simonyiszk/open-hf-sdr/DOC/if3_filter.asc

C1: cap; 166p
C2: cap; 940p
C3: cap; 18p
C4: cap; 213p
L1: ind; 2.2µ
L2: ind; 10µ
L3: ind; 1.1µ
L5: ind; 220n
RL: res; 50
V1: voltage; ""; AC 1 0; Rser=1500
Named nets: 0
.ac lin 1001 5Meg 15Meg
.net I(RL) V1
4th Order Inverse Chebyshev Bandpass
Conventional, Series First
Lower Cutoff Freq. = 35.25 MHz; Upper Cutoff Freq. = 38.75 MHz
Stopband Attenuation = 50.00 dB

rf-tools.com | Dec 27 2020 18:43
.step param C 2.2u 2.4u 200n
