simonyiszk/open-hf-sdr/DOC/cb_diff_amp.asc

C1: cap; 56p
C2: cap; 22p
C3: cap; 270p
C4: cap; 33p
C5: cap; 33p
C6: cap; 330p
C7: cap; 330p
C8: cap; 10µ
C9: cap; 7.96p
L1: ind; 3.3µ
L2: ind; 3.3µ
L3: ind; 10µ
L4: ind; 10µ
L5: ind; 1.5µ
L6: ind; 150n
L7: ind; 150n
L8: ind; 19.65µ
L9: ind; 19.65µ
Q1: npn
Q2: npn
R1: res; 2k
R2: res; 1500
R3: res; 1500
R4: res; 10k
R5: res; 10k
V1: voltage; ""; AC 1
V2: voltage; ""; AC 1
V3: voltage; 2.8
V4: voltage; 5
Named nets: In+, In-, 0, Out+, Out-
.ac lin 100meg 5meg 15meg
;op lin 1meg 5meg 15meg
