simonyiszk/open-hf-sdr/vivado/ha5kfu_ws2/ha5kfu_ws2.srcs/sources_1/bd/top/ip/top_dds_compiler_0_0/synth/top_dds_compiler_0_0.vhd

-- (c) Copyright 1995-2021 Xilinx, Inc. All rights reserved.
-- 
-- This file contains confidential and proprietary information
-- of Xilinx, Inc. and is protected under U.S. and
-- international copyright and other intellectual property
-- laws.
-- 
-- DISCLAIMER
-- This disclaimer is not a license and does not grant any
-- rights to the materials distributed herewith. Except as
-- otherwise provided in a valid license issued to you by
-- Xilinx, and to the maximum extent permitted by applicable
-- law: (1) THESE MATERIALS ARE MADE AVAILABLE "AS IS" AND
-- WITH ALL FAULTS, AND XILINX HEREBY DISCLAIMS ALL WARRANTIES
-- AND CONDITIONS, EXPRESS, IMPLIED, OR STATUTORY, INCLUDING
-- BUT NOT LIMITED TO WARRANTIES OF MERCHANTABILITY, NON-
-- INFRINGEMENT, OR FITNESS FOR ANY PARTICULAR PURPOSE; and
-- (2) Xilinx shall not be liable (whether in contract or tort,
-- including negligence, or under any other theory of
-- liability) for any loss or damage of any kind or nature
-- related to, arising under or in connection with these
-- materials, including for any direct, or any indirect,
-- special, incidental, or consequential loss or damage
-- (including loss of data, profits, goodwill, or any type of
-- loss or damage suffered as a result of any action brought
-- by a third party) even if such damage or loss was
-- reasonably foreseeable or Xilinx had been advised of the
-- possibility of the same.
-- 
-- CRITICAL APPLICATIONS
-- Xilinx products are not designed or intended to be fail-
-- safe, or for use in any application requiring fail-safe
-- performance, such as life-support or safety devices or
-- systems, Class III medical devices, nuclear facilities,
-- applications related to the deployment of airbags, or any
-- other applications that could lead to death, personal
-- injury, or severe property or environmental damage
-- (individually and collectively, "Critical
-- Applications"). Customer assumes the sole risk and
-- liability of any use of Xilinx products in Critical
-- Applications, subject only to applicable laws and
-- regulations governing limitations on product liability.
-- 
-- THIS COPYRIGHT NOTICE AND DISCLAIMER MUST BE RETAINED AS
-- PART OF THIS FILE AT ALL TIMES.
-- 
-- DO NOT MODIFY THIS FILE.

-- IP VLNV: xilinx.com:ip:dds_compiler:6.0
-- IP Revision: 20

LIBRARY ieee;
USE ieee.std_logic_1164.ALL;
USE ieee.numeric_std.ALL;

LIBRARY dds_compiler_v6_0_20;
USE dds_compiler_v6_0_20.dds_compiler_v6_0_20;

ENTITY top_dds_compiler_0_0 IS
  PORT (
    aclk : IN STD_LOGIC;
    s_axis_config_tvalid : IN STD_LOGIC;
    s_axis_config_tdata : IN STD_LOGIC_VECTOR(63 DOWNTO 0);
    m_axis_data_tvalid : OUT STD_LOGIC;
    m_axis_data_tdata : OUT STD_LOGIC_VECTOR(15 DOWNTO 0);
    m_axis_phase_tvalid : OUT STD_LOGIC;
    m_axis_phase_tdata : OUT STD_LOGIC_VECTOR(31 DOWNTO 0)
  );
END top_dds_compiler_0_0;

ARCHITECTURE top_dds_compiler_0_0_arch OF top_dds_compiler_0_0 IS
  ATTRIBUTE DowngradeIPIdentifiedWarnings : STRING;
  ATTRIBUTE DowngradeIPIdentifiedWarnings OF top_dds_compiler_0_0_arch: ARCHITECTURE IS "yes";
  COMPONENT dds_compiler_v6_0_20 IS
    GENERIC (
      C_XDEVICEFAMILY : STRING;
      C_MODE_OF_OPERATION : INTEGER;
      C_MODULUS : INTEGER;
      C_ACCUMULATOR_WIDTH : INTEGER;
      C_CHANNELS : INTEGER;
      C_HAS_PHASE_OUT : INTEGER;
      C_HAS_PHASEGEN : INTEGER;
      C_HAS_SINCOS : INTEGER;
      C_LATENCY : INTEGER;
      C_MEM_TYPE : INTEGER;
      C_NEGATIVE_COSINE : INTEGER;
      C_NEGATIVE_SINE : INTEGER;
      C_NOISE_SHAPING : INTEGER;
      C_OUTPUTS_REQUIRED : INTEGER;
      C_OUTPUT_FORM : INTEGER;
      C_OUTPUT_WIDTH : INTEGER;
      C_PHASE_ANGLE_WIDTH : INTEGER;
      C_PHASE_INCREMENT : INTEGER;
      C_PHASE_INCREMENT_VALUE : STRING;
      C_RESYNC : INTEGER;
      C_PHASE_OFFSET : INTEGER;
      C_PHASE_OFFSET_VALUE : STRING;
      C_OPTIMISE_GOAL : INTEGER;
      C_USE_DSP48 : INTEGER;
      C_POR_MODE : INTEGER;
      C_AMPLITUDE : INTEGER;
      C_HAS_ACLKEN : INTEGER;
      C_HAS_ARESETN : INTEGER;
      C_HAS_TLAST : INTEGER;
      C_HAS_TREADY : INTEGER;
      C_HAS_S_PHASE : INTEGER;
      C_S_PHASE_TDATA_WIDTH : INTEGER;
      C_S_PHASE_HAS_TUSER : INTEGER;
      C_S_PHASE_TUSER_WIDTH : INTEGER;
      C_HAS_S_CONFIG : INTEGER;
      C_S_CONFIG_SYNC_MODE : INTEGER;
      C_S_CONFIG_TDATA_WIDTH : INTEGER;
      C_HAS_M_DATA : INTEGER;
      C_M_DATA_TDATA_WIDTH : INTEGER;
      C_M_DATA_HAS_TUSER : INTEGER;
      C_M_DATA_TUSER_WIDTH : INTEGER;
      C_HAS_M_PHASE : INTEGER;
      C_M_PHASE_TDATA_WIDTH : INTEGER;
      C_M_PHASE_HAS_TUSER : INTEGER;
      C_M_PHASE_TUSER_WIDTH : INTEGER;
      C_DEBUG_INTERFACE : INTEGER;
      C_CHAN_WIDTH : INTEGER
    );
    PORT (
      aclk : IN STD_LOGIC;
      aclken : IN STD_LOGIC;
      aresetn : IN STD_LOGIC;
      s_axis_phase_tvalid : IN STD_LOGIC;
      s_axis_phase_tready : OUT STD_LOGIC;
      s_axis_phase_tdata : IN STD_LOGIC_VECTOR(0 DOWNTO 0);
      s_axis_phase_tlast : IN STD_LOGIC;
      s_axis_phase_tuser : IN STD_LOGIC_VECTOR(0 DOWNTO 0);
      s_axis_config_tvalid : IN STD_LOGIC;
      s_axis_config_tready : OUT STD_LOGIC;
      s_axis_config_tdata : IN STD_LOGIC_VECTOR(63 DOWNTO 0);
      s_axis_config_tlast : IN STD_LOGIC;
      m_axis_data_tvalid : OUT STD_LOGIC;
      m_axis_data_tready : IN STD_LOGIC;
      m_axis_data_tdata : OUT STD_LOGIC_VECTOR(15 DOWNTO 0);
      m_axis_data_tlast : OUT STD_LOGIC;
      m_axis_data_tuser : OUT STD_LOGIC_VECTOR(0 DOWNTO 0);
      m_axis_phase_tvalid : OUT STD_LOGIC;
      m_axis_phase_tready : IN STD_LOGIC;
      m_axis_phase_tdata : OUT STD_LOGIC_VECTOR(31 DOWNTO 0);
      m_axis_phase_tlast : OUT STD_LOGIC;
      m_axis_phase_tuser : OUT STD_LOGIC_VECTOR(0 DOWNTO 0);
      event_pinc_invalid : OUT STD_LOGIC;
      event_poff_invalid : OUT STD_LOGIC;
      event_phase_in_invalid : OUT STD_LOGIC;
      event_s_phase_tlast_missing : OUT STD_LOGIC;
      event_s_phase_tlast_unexpected : OUT STD_LOGIC;
      event_s_phase_chanid_incorrect : OUT STD_LOGIC;
      event_s_config_tlast_missing : OUT STD_LOGIC;
      event_s_config_tlast_unexpected : OUT STD_LOGIC
    );
  END COMPONENT dds_compiler_v6_0_20;
  ATTRIBUTE X_CORE_INFO : STRING;
  ATTRIBUTE X_CORE_INFO OF top_dds_compiler_0_0_arch: ARCHITECTURE IS "dds_compiler_v6_0_20,Vivado 2020.2";
  ATTRIBUTE CHECK_LICENSE_TYPE : STRING;
  ATTRIBUTE CHECK_LICENSE_TYPE OF top_dds_compiler_0_0_arch : ARCHITECTURE IS "top_dds_compiler_0_0,dds_compiler_v6_0_20,{}";
  ATTRIBUTE CORE_GENERATION_INFO : STRING;
  ATTRIBUTE CORE_GENERATION_INFO OF top_dds_compiler_0_0_arch: ARCHITECTURE IS "top_dds_compiler_0_0,dds_compiler_v6_0_20,{x_ipProduct=Vivado 2020.2,x_ipVendor=xilinx.com,x_ipLibrary=ip,x_ipName=dds_compiler,x_ipVersion=6.0,x_ipCoreRevision=20,x_ipLanguage=VERILOG,x_ipSimLanguage=MIXED,C_XDEVICEFAMILY=spartan7,C_MODE_OF_OPERATION=0,C_MODULUS=9,C_ACCUMULATOR_WIDTH=27,C_CHANNELS=1,C_HAS_PHASE_OUT=1,C_HAS_PHASEGEN=1,C_HAS_SINCOS=1,C_LATENCY=4,C_MEM_TYPE=1,C_NEGATIVE_COSINE=0,C_NEGATIVE_SINE=0,C_NOISE_SHAPING=0,C_OUTPUTS_REQUIRED=2,C_OUTPUT_FORM=0,C_OUTPUT_WIDTH=8,C_PHASE_ANGLE" & 
"_WIDTH=8,C_PHASE_INCREMENT=1,C_PHASE_INCREMENT_VALUE=0_0_0_0_0_0_0_0_0_0_0_0_0_0_0_0,C_RESYNC=0,C_PHASE_OFFSET=1,C_PHASE_OFFSET_VALUE=0_0_0_0_0_0_0_0_0_0_0_0_0_0_0_0,C_OPTIMISE_GOAL=0,C_USE_DSP48=0,C_POR_MODE=0,C_AMPLITUDE=0,C_HAS_ACLKEN=0,C_HAS_ARESETN=0,C_HAS_TLAST=0,C_HAS_TREADY=0,C_HAS_S_PHASE=0,C_S_PHASE_TDATA_WIDTH=1,C_S_PHASE_HAS_TUSER=0,C_S_PHASE_TUSER_WIDTH=1,C_HAS_S_CONFIG=1,C_S_CONFIG_SYNC_MODE=0,C_S_CONFIG_TDATA_WIDTH=64,C_HAS_M_DATA=1,C_M_DATA_TDATA_WIDTH=16,C_M_DATA_HAS_TUSER=0,C_M" & 
"_DATA_TUSER_WIDTH=1,C_HAS_M_PHASE=1,C_M_PHASE_TDATA_WIDTH=32,C_M_PHASE_HAS_TUSER=0,C_M_PHASE_TUSER_WIDTH=1,C_DEBUG_INTERFACE=0,C_CHAN_WIDTH=1}";
  ATTRIBUTE X_INTERFACE_INFO : STRING;
  ATTRIBUTE X_INTERFACE_PARAMETER : STRING;
  ATTRIBUTE X_INTERFACE_INFO OF m_axis_phase_tdata: SIGNAL IS "xilinx.com:interface:axis:1.0 M_AXIS_PHASE TDATA";
  ATTRIBUTE X_INTERFACE_PARAMETER OF m_axis_phase_tvalid: SIGNAL IS "XIL_INTERFACENAME M_AXIS_PHASE, TDATA_NUM_BYTES 4, TDEST_WIDTH 0, TID_WIDTH 0, TUSER_WIDTH 0, HAS_TREADY 0, HAS_TSTRB 0, HAS_TKEEP 0, HAS_TLAST 0, FREQ_HZ 125000000, PHASE 0.000, CLK_DOMAIN top_clk, LAYERED_METADATA xilinx.com:interface:datatypes:1.0 {TDATA {datatype {name {attribs {resolve_type immediate dependency {} format string minimum {} maximum {}} value {}} bitwidth {attribs {resolve_type automatic dependency {} format long minimum {} maximum {}} value 27} bitoffset {attribs {resolve_typ" & 
"e immediate dependency {} format long minimum {} maximum {}} value 0} array_type {name {attribs {resolve_type immediate dependency {} format string minimum {} maximum {}} value chan} size {attribs {resolve_type generated dependency chan_size format long minimum {} maximum {}} value 1} stride {attribs {resolve_type generated dependency chan_stride format long minimum {} maximum {}} value 32} datatype {name {attribs {resolve_type immediate dependency {} format string minimum {} maximum {}} value {" & 
"}} bitwidth {attribs {resolve_type automatic dependency {} format long minimum {} maximum {}} value 27} bitoffset {attribs {resolve_type immediate dependency {} format long minimum {} maximum {}} value 0} struct {field_phase_out {name {attribs {resolve_type immediate dependency {} format string minimum {} maximum {}} value phase_out} enabled {attribs {resolve_type immediate dependency {} format bool minimum {} maximum {}} value true} datatype {name {attribs {resolve_type immediate dependency {} " & 
"format string minimum {} maximum {}} value {}} bitwidth {attribs {resolve_type generated dependency phase_width format long minimum {} maximum {}} value 27} bitoffset {attribs {resolve_type immediate dependency {} format long minimum {} maximum {}} value 0} real {fixed {fractwidth {attribs {resolve_type generated dependency phase_fractwidth format long minimum {} maximum {}} value 27} signed {attribs {resolve_type immediate dependency {} format bool minimum {} maximum {}} value false}}}}}}}}}} T" & 
"DATA_WIDTH 32 TUSER {datatype {name {attribs {resolve_type immediate dependency {} format string minimum {} maximum {}} value {}} bitwidth {attribs {resolve_type automatic dependency {} format long minimum {} maximum {}} value 0} bitoffset {attribs {resolve_type immediate dependency {} format long minimum {} maximum {}} value 0} struct {field_chanid {name {attribs {resolve_type immediate dependency {} format string minimum {} maximum {}} value chanid} enabled {attribs {resolve_type generated dep" & 
"endency chanid_enabled format bool minimum {} maximum {}} value false} datatype {name {attribs {resolve_type immediate dependency {} format string minimum {} maximum {}} value {}} bitwidth {attribs {resolve_type generated dependency chanid_width format long minimum {} maximum {}} value 0} bitoffset {attribs {resolve_type immediate dependency {} format long minimum {} maximum {}} value 0} integer {signed {attribs {resolve_type immediate dependency {} format bool minimum {} maximum {}} value false" & 
"}}}} field_user {name {attribs {resolve_type immediate dependency {} format string minimum {} maximum {}} value user} enabled {attribs {resolve_type generated dependency user_enabled format bool minimum {} maximum {}} value false} datatype {name {attribs {resolve_type immediate dependency {} format string minimum {} maximum {}} value {}} bitwidth {attribs {resolve_type generated dependency user_width format long minimum {} maximum {}} value 0} bitoffset {attribs {resolve_type generated dependenc" & 
"y user_offset format long minimum {} maximum {}} value 0}}}}}} TUSER_WIDTH 0}, INSERT_VIP 0";
  ATTRIBUTE X_INTERFACE_INFO OF m_axis_phase_tvalid: SIGNAL IS "xilinx.com:interface:axis:1.0 M_AXIS_PHASE TVALID";
  ATTRIBUTE X_INTERFACE_INFO OF m_axis_data_tdata: SIGNAL IS "xilinx.com:interface:axis:1.0 M_AXIS_DATA TDATA";
  ATTRIBUTE X_INTERFACE_PARAMETER OF m_axis_data_tvalid: SIGNAL IS "XIL_INTERFACENAME M_AXIS_DATA, TDATA_NUM_BYTES 2, TDEST_WIDTH 0, TID_WIDTH 0, TUSER_WIDTH 0, HAS_TREADY 0, HAS_TSTRB 0, HAS_TKEEP 0, HAS_TLAST 0, FREQ_HZ 125000000, PHASE 0.000, CLK_DOMAIN top_clk, LAYERED_METADATA xilinx.com:interface:datatypes:1.0 {TDATA {datatype {name {attribs {resolve_type immediate dependency {} format string minimum {} maximum {}} value {}} bitwidth {attribs {resolve_type automatic dependency {} format long minimum {} maximum {}} value 16} bitoffset {attribs {resolve_type" & 
" immediate dependency {} format long minimum {} maximum {}} value 0} array_type {name {attribs {resolve_type immediate dependency {} format string minimum {} maximum {}} value chan} size {attribs {resolve_type generated dependency chan_size format long minimum {} maximum {}} value 1} stride {attribs {resolve_type generated dependency chan_stride format long minimum {} maximum {}} value 16} datatype {name {attribs {resolve_type immediate dependency {} format string minimum {} maximum {}} value {}" & 
"} bitwidth {attribs {resolve_type automatic dependency {} format long minimum {} maximum {}} value 16} bitoffset {attribs {resolve_type immediate dependency {} format long minimum {} maximum {}} value 0} struct {field_cosine {name {attribs {resolve_type immediate dependency {} format string minimum {} maximum {}} value cosine} enabled {attribs {resolve_type generated dependency cosine_enabled format bool minimum {} maximum {}} value true} datatype {name {attribs {resolve_type immediate dependenc" & 
"y {} format string minimum {} maximum {}} value {}} bitwidth {attribs {resolve_type generated dependency cosine_width format long minimum {} maximum {}} value 8} bitoffset {attribs {resolve_type immediate dependency {} format long minimum {} maximum {}} value 0} real {fixed {fractwidth {attribs {resolve_type generated dependency cosine_fractwidth format long minimum {} maximum {}} value 7} signed {attribs {resolve_type immediate dependency {} format bool minimum {} maximum {}} value true}}}}} fi" & 
"eld_sine {name {attribs {resolve_type immediate dependency {} format string minimum {} maximum {}} value sine} enabled {attribs {resolve_type generated dependency sine_enabled format bool minimum {} maximum {}} value true} datatype {name {attribs {resolve_type immediate dependency {} format string minimum {} maximum {}} value {}} bitwidth {attribs {resolve_type generated dependency sine_width format long minimum {} maximum {}} value 8} bitoffset {attribs {resolve_type generated dependency sine_o" & 
"ffset format long minimum {} maximum {}} value 8} real {fixed {fractwidth {attribs {resolve_type generated dependency sine_fractwidth format long minimum {} maximum {}} value 7} signed {attribs {resolve_type immediate dependency {} format bool minimum {} maximum {}} value true}}}}}}}}}} TDATA_WIDTH 16 TUSER {datatype {name {attribs {resolve_type immediate dependency {} format string minimum {} maximum {}} value {}} bitwidth {attribs {resolve_type automatic dependency {} format long minimum {} ma" & 
"ximum {}} value 0} bitoffset {attribs {resolve_type immediate dependency {} format long minimum {} maximum {}} value 0} struct {field_chanid {name {attribs {resolve_type immediate dependency {} format string minimum {} maximum {}} value chanid} enabled {attribs {resolve_type generated dependency chanid_enabled format bool minimum {} maximum {}} value false} datatype {name {attribs {resolve_type immediate dependency {} format string minimum {} maximum {}} value {}} bitwidth {attribs {resolve_type" & 
" generated dependency chanid_width format long minimum {} maximum {}} value 0} bitoffset {attribs {resolve_type immediate dependency {} format long minimum {} maximum {}} value 0} integer {signed {attribs {resolve_type immediate dependency {} format bool minimum {} maximum {}} value false}}}} field_user {name {attribs {resolve_type immediate dependency {} format string minimum {} maximum {}} value user} enabled {attribs {resolve_type generated dependency user_enabled format bool minimum {} maxim" & 
"um {}} value false} datatype {name {attribs {resolve_type immediate dependency {} format string minimum {} maximum {}} value {}} bitwidth {attribs {resolve_type generated dependency user_width format long minimum {} maximum {}} value 0} bitoffset {attribs {resolve_type generated dependency user_offset format long minimum {} maximum {}} value 0}}}}}} TUSER_WIDTH 0}, INSERT_VIP 0";
  ATTRIBUTE X_INTERFACE_INFO OF m_axis_data_tvalid: SIGNAL IS "xilinx.com:interface:axis:1.0 M_AXIS_DATA TVALID";
  ATTRIBUTE X_INTERFACE_INFO OF s_axis_config_tdata: SIGNAL IS "xilinx.com:interface:axis:1.0 S_AXIS_CONFIG TDATA";
  ATTRIBUTE X_INTERFACE_PARAMETER OF s_axis_config_tvalid: SIGNAL IS "XIL_INTERFACENAME S_AXIS_CONFIG, TDATA_NUM_BYTES 8, TDEST_WIDTH 0, TID_WIDTH 0, TUSER_WIDTH 0, HAS_TREADY 0, HAS_TSTRB 0, HAS_TKEEP 0, HAS_TLAST 0, FREQ_HZ 125000000, PHASE 0.000, CLK_DOMAIN top_clk, LAYERED_METADATA undef, INSERT_VIP 0";
  ATTRIBUTE X_INTERFACE_INFO OF s_axis_config_tvalid: SIGNAL IS "xilinx.com:interface:axis:1.0 S_AXIS_CONFIG TVALID";
  ATTRIBUTE X_INTERFACE_PARAMETER OF aclk: SIGNAL IS "XIL_INTERFACENAME aclk_intf, ASSOCIATED_BUSIF M_AXIS_PHASE:S_AXIS_CONFIG:M_AXIS_DATA:S_AXIS_PHASE, ASSOCIATED_RESET aresetn, ASSOCIATED_CLKEN aclken, FREQ_HZ 125000000, FREQ_TOLERANCE_HZ 0, PHASE 0.000, CLK_DOMAIN top_clk, INSERT_VIP 0";
  ATTRIBUTE X_INTERFACE_INFO OF aclk: SIGNAL IS "xilinx.com:signal:clock:1.0 aclk_intf CLK";
BEGIN
  U0 : dds_compiler_v6_0_20
    GENERIC MAP (
      C_XDEVICEFAMILY => "spartan7",
      C_MODE_OF_OPERATION => 0,
      C_MODULUS => 9,
      C_ACCUMULATOR_WIDTH => 27,
      C_CHANNELS => 1,
      C_HAS_PHASE_OUT => 1,
      C_HAS_PHASEGEN => 1,
      C_HAS_SINCOS => 1,
      C_LATENCY => 4,
      C_MEM_TYPE => 1,
      C_NEGATIVE_COSINE => 0,
      C_NEGATIVE_SINE => 0,
      C_NOISE_SHAPING => 0,
      C_OUTPUTS_REQUIRED => 2,
      C_OUTPUT_FORM => 0,
      C_OUTPUT_WIDTH => 8,
      C_PHASE_ANGLE_WIDTH => 8,
      C_PHASE_INCREMENT => 1,
      C_PHASE_INCREMENT_VALUE => "0,0,0,0,0,0,0,0,0,0,0,0,0,0,0,0",
      C_RESYNC => 0,
      C_PHASE_OFFSET => 1,
      C_PHASE_OFFSET_VALUE => "0,0,0,0,0,0,0,0,0,0,0,0,0,0,0,0",
      C_OPTIMISE_GOAL => 0,
      C_USE_DSP48 => 0,
      C_POR_MODE => 0,
      C_AMPLITUDE => 0,
      C_HAS_ACLKEN => 0,
      C_HAS_ARESETN => 0,
      C_HAS_TLAST => 0,
      C_HAS_TREADY => 0,
      C_HAS_S_PHASE => 0,
      C_S_PHASE_TDATA_WIDTH => 1,
      C_S_PHASE_HAS_TUSER => 0,
      C_S_PHASE_TUSER_WIDTH => 1,
      C_HAS_S_CONFIG => 1,
      C_S_CONFIG_SYNC_MODE => 0,
      C_S_CONFIG_TDATA_WIDTH => 64,
      C_HAS_M_DATA => 1,
      C_M_DATA_TDATA_WIDTH => 16,
      C_M_DATA_HAS_TUSER => 0,
      C_M_DATA_TUSER_WIDTH => 1,
      C_HAS_M_PHASE => 1,
      C_M_PHASE_TDATA_WIDTH => 32,
      C_M_PHASE_HAS_TUSER => 0,
      C_M_PHASE_TUSER_WIDTH => 1,
      C_DEBUG_INTERFACE => 0,
      C_CHAN_WIDTH => 1
    )
    PORT MAP (
      aclk => aclk,
      aclken => '1',
      aresetn => '1',
      s_axis_phase_tvalid => '0',
      s_axis_phase_tdata => STD_LOGIC_VECTOR(TO_UNSIGNED(0, 1)),
      s_axis_phase_tlast => '0',
      s_axis_phase_tuser => STD_LOGIC_VECTOR(TO_UNSIGNED(0, 1)),
      s_axis_config_tvalid => s_axis_config_tvalid,
      s_axis_config_tdata => s_axis_config_tdata,
      s_axis_config_tlast => '0',
      m_axis_data_tvalid => m_axis_data_tvalid,
      m_axis_data_tready => '0',
      m_axis_data_tdata => m_axis_data_tdata,
      m_axis_phase_tvalid => m_axis_phase_tvalid,
      m_axis_phase_tready => '0',
      m_axis_phase_tdata => m_axis_phase_tdata
    );
END top_dds_compiler_0_0_arch;
