simonyiszk/open-hf-sdr/vivado/ha5kfu_ws2/ha5kfu_ws2.srcs/sources_1/bd/top/ip/top_c_addsub_0_0/top_c_addsub_0_0_stub.vhdl

-- Copyright 1986-2020 Xilinx, Inc. All Rights Reserved.
-- --------------------------------------------------------------------------------
-- Tool Version: Vivado v.2020.2 (win64) Build 3064766 Wed Nov 18 09:12:45 MST 2020
-- Date        : Fri Feb 12 23:06:54 2021
-- Host        : RemoteApp running 64-bit major release  (build 9200)
-- Command     : write_vhdl -force -mode synth_stub -rename_top top_c_addsub_0_0 -prefix
--               top_c_addsub_0_0_ top_c_addsub_0_0_stub.vhdl
-- Design      : top_c_addsub_0_0
-- Purpose     : Stub declaration of top-level module interface
-- Device      : xc7s6ftgb196-1
-- --------------------------------------------------------------------------------
library IEEE;
use IEEE.STD_LOGIC_1164.ALL;

entity top_c_addsub_0_0 is
  Port ( 
    A : in STD_LOGIC_VECTOR ( 12 downto 0 );
    B : in STD_LOGIC_VECTOR ( 12 downto 0 );
    CLK : in STD_LOGIC;
    S : out STD_LOGIC_VECTOR ( 13 downto 0 )
  );

end top_c_addsub_0_0;

architecture stub of top_c_addsub_0_0 is
attribute syn_black_box : boolean;
attribute black_box_pad_pin : string;
attribute syn_black_box of stub : architecture is true;
attribute black_box_pad_pin of stub : architecture is "A[12:0],B[12:0],CLK,S[13:0]";
attribute x_core_info : string;
attribute x_core_info of stub : architecture is "c_addsub_v12_0_14,Vivado 2020.2";
begin
end;
