simonyiszk/open-hf-sdr/vivado/ha5kfu_ws2/ha5kfu_ws2.srcs/sources_1/bd/top_design/ip/top_design_mult_gen_0_3/top_design_mult_gen_0_3_stub.vhdl

-- Copyright 1986-2020 Xilinx, Inc. All Rights Reserved.
-- --------------------------------------------------------------------------------
-- Tool Version: Vivado v.2020.2 (win64) Build 3064766 Wed Nov 18 09:12:45 MST 2020
-- Date        : Fri Feb 12 22:11:44 2021
-- Host        : RemoteApp running 64-bit major release  (build 9200)
-- Command     : write_vhdl -force -mode synth_stub -rename_top top_design_mult_gen_0_3 -prefix
--               top_design_mult_gen_0_3_ top_design_mult_gen_0_1_stub.vhdl
-- Design      : top_design_mult_gen_0_1
-- Purpose     : Stub declaration of top-level module interface
-- Device      : xc7z010clg400-1
-- --------------------------------------------------------------------------------
library IEEE;
use IEEE.STD_LOGIC_1164.ALL;

entity top_design_mult_gen_0_3 is
  Port ( 
    CLK : in STD_LOGIC;
    A : in STD_LOGIC_VECTOR ( 13 downto 0 );
    B : in STD_LOGIC_VECTOR ( 7 downto 0 );
    P : out STD_LOGIC_VECTOR ( 12 downto 0 )
  );

end top_design_mult_gen_0_3;

architecture stub of top_design_mult_gen_0_3 is
attribute syn_black_box : boolean;
attribute black_box_pad_pin : string;
attribute syn_black_box of stub : architecture is true;
attribute black_box_pad_pin of stub : architecture is "CLK,A[13:0],B[7:0],P[12:0]";
attribute x_core_info : string;
attribute x_core_info of stub : architecture is "mult_gen_v12_0_16,Vivado 2020.2";
begin
end;
