simonyiszk/open-hf-sdr/vivado/ha5kfu_ws2/ha5kfu_ws2.srcs/sources_1/bd/top/ip/top_c_addsub_0_0/top_c_addsub_0_0_sim_netlist.v

// Copyright 1986-2020 Xilinx, Inc. All Rights Reserved.
// --------------------------------------------------------------------------------
// Tool Version: Vivado v.2020.2 (win64) Build 3064766 Wed Nov 18 09:12:45 MST 2020
// Date        : Fri Feb 12 23:06:54 2021
// Host        : RemoteApp running 64-bit major release  (build 9200)
// Command     : write_verilog -force -mode funcsim -rename_top top_c_addsub_0_0 -prefix
//               top_c_addsub_0_0_ top_c_addsub_0_0_sim_netlist.v
// Design      : top_c_addsub_0_0
// Purpose     : This verilog netlist is a functional simulation representation of the design and should not be modified
//               or synthesized. This netlist cannot be used for SDF annotated simulation.
// Device      : xc7s6ftgb196-1
// --------------------------------------------------------------------------------
`timescale 1 ps / 1 ps

(* CHECK_LICENSE_TYPE = "top_c_addsub_0_0,c_addsub_v12_0_14,{}" *) (* downgradeipidentifiedwarnings = "yes" *) (* x_core_info = "c_addsub_v12_0_14,Vivado 2020.2" *) 
(* NotValidForBitStream *)
module top_c_addsub_0_0
   (A,
    B,
    CLK,
    S);
  (* x_interface_info = "xilinx.com:signal:data:1.0 a_intf DATA" *) (* x_interface_parameter = "XIL_INTERFACENAME a_intf, LAYERED_METADATA xilinx.com:interface:datatypes:1.0 {DATA {datatype {name {attribs {resolve_type immediate dependency {} format string minimum {} maximum {}} value data} bitwidth {attribs {resolve_type generated dependency bitwidth format long minimum {} maximum {}} value 13} bitoffset {attribs {resolve_type immediate dependency {} format long minimum {} maximum {}} value 0} integer {signed {attribs {resolve_type generated dependency signed format bool minimum {} maximum {}} value TRUE}}}} DATA_WIDTH 13}" *) input [12:0]A;
  (* x_interface_info = "xilinx.com:signal:data:1.0 b_intf DATA" *) (* x_interface_parameter = "XIL_INTERFACENAME b_intf, LAYERED_METADATA xilinx.com:interface:datatypes:1.0 {DATA {datatype {name {attribs {resolve_type immediate dependency {} format string minimum {} maximum {}} value data} bitwidth {attribs {resolve_type generated dependency bitwidth format long minimum {} maximum {}} value 13} bitoffset {attribs {resolve_type immediate dependency {} format long minimum {} maximum {}} value 0} integer {signed {attribs {resolve_type generated dependency signed format bool minimum {} maximum {}} value TRUE}}}} DATA_WIDTH 13}" *) input [12:0]B;
  (* x_interface_info = "xilinx.com:signal:clock:1.0 clk_intf CLK" *) (* x_interface_parameter = "XIL_INTERFACENAME clk_intf, ASSOCIATED_BUSIF s_intf:c_out_intf:sinit_intf:sset_intf:bypass_intf:c_in_intf:add_intf:b_intf:a_intf, ASSOCIATED_RESET SCLR, ASSOCIATED_CLKEN CE, FREQ_HZ 125000000, FREQ_TOLERANCE_HZ 0, PHASE 0.000, CLK_DOMAIN top_clk, INSERT_VIP 0" *) input CLK;
  (* x_interface_info = "xilinx.com:signal:data:1.0 s_intf DATA" *) (* x_interface_parameter = "XIL_INTERFACENAME s_intf, LAYERED_METADATA xilinx.com:interface:datatypes:1.0 {DATA {datatype {name {attribs {resolve_type immediate dependency {} format string minimum {} maximum {}} value data} bitwidth {attribs {resolve_type generated dependency bitwidth format long minimum {} maximum {}} value 14} bitoffset {attribs {resolve_type immediate dependency {} format long minimum {} maximum {}} value 0} integer {signed {attribs {resolve_type generated dependency signed format bool minimum {} maximum {}} value TRUE}}}} DATA_WIDTH 14}" *) output [13:0]S;

  wire [12:0]A;
  wire [12:0]B;
  wire CLK;
  wire [13:0]S;
  wire NLW_U0_C_OUT_UNCONNECTED;

  (* C_AINIT_VAL = "0" *) 
  (* C_BORROW_LOW = "1" *) 
  (* C_CE_OVERRIDES_BYPASS = "1" *) 
  (* C_CE_OVERRIDES_SCLR = "0" *) 
  (* C_HAS_CE = "0" *) 
  (* C_HAS_SCLR = "0" *) 
  (* C_HAS_SINIT = "0" *) 
  (* C_HAS_SSET = "0" *) 
  (* C_IMPLEMENTATION = "0" *) 
  (* C_SCLR_OVERRIDES_SSET = "1" *) 
  (* C_SINIT_VAL = "0" *) 
  (* C_VERBOSITY = "0" *) 
  (* C_XDEVICEFAMILY = "spartan7" *) 
  (* c_a_type = "0" *) 
  (* c_a_width = "13" *) 
  (* c_add_mode = "0" *) 
  (* c_b_constant = "0" *) 
  (* c_b_type = "0" *) 
  (* c_b_value = "0000000000000" *) 
  (* c_b_width = "13" *) 
  (* c_bypass_low = "0" *) 
  (* c_has_bypass = "0" *) 
  (* c_has_c_in = "0" *) 
  (* c_has_c_out = "0" *) 
  (* c_latency = "1" *) 
  (* c_out_width = "14" *) 
  (* downgradeipidentifiedwarnings = "yes" *) 
  (* is_du_within_envelope = "true" *) 
  top_c_addsub_0_0_c_addsub_v12_0_14 U0
       (.A(A),
        .ADD(1'b1),
        .B(B),
        .BYPASS(1'b0),
        .CE(1'b1),
        .CLK(CLK),
        .C_IN(1'b0),
        .C_OUT(NLW_U0_C_OUT_UNCONNECTED),
        .S(S),
        .SCLR(1'b0),
        .SINIT(1'b0),
        .SSET(1'b0));
endmodule
`pragma protect begin_protected
`pragma protect version = 1
`pragma protect encrypt_agent = "XILINX"
`pragma protect encrypt_agent_info = "Xilinx Encryption Tool 2020.2"
`pragma protect key_keyowner="Cadence Design Systems.", key_keyname="cds_rsa_key", key_method="rsa"
`pragma protect encoding = (enctype="BASE64", line_length=76, bytes=64)
`pragma protect key_block
R+TTV2BAhe9Ek8IveLCAIK+vyB2qa4TorazWyGCbrxCKkVhTBvAD6RqPeP/JqtRuh2zDPzraR9rT
gUyNSWD83A==

`pragma protect key_keyowner="Synopsys", key_keyname="SNPS-VCS-RSA-2", key_method="rsa"
`pragma protect encoding = (enctype="BASE64", line_length=76, bytes=128)
`pragma protect key_block
XM2mYTm+gCT0AhW4S5p7IlzH34WHm/fa2tLSENK5xQp44huwLBqk+dBcYbe4GM+6wqA3pzoUNE9T
SluI3P6DpsOt14ispiaJSciB+VdlU+Q0e63sKyfq++TGO3CTW5OhLIxojUbYrTbdY4WbGkk4yG0Y
qGwauBBx1uBueCA2GC4=

`pragma protect key_keyowner="Aldec", key_keyname="ALDEC15_001", key_method="rsa"
`pragma protect encoding = (enctype="BASE64", line_length=76, bytes=256)
`pragma protect key_block
M9U+BjMD5E96pT2zTDB1OSiHn8IS+G+aDNa3MIF/jeClLSPAOJwufjuzRcyAtwx0354Pb7AaFOwR
6CcoWPQM1dcUC6avyG/0PRrtZP/KpXS3/9PiWsaFHPYVLfqBMCUDoraXwfpfMxmOy8hD0iI6TtWc
j1xJUXVsbv+kqOeTUloYmwdRx/8cs46FvZfnFpiZXMFMsTsT9zvmCyNxiZefgFKT064BWsCkg2fa
W2IXperFJQzpE9mXVwGSjl6xDUp55esPyEPcDI4xy0T+q2KtBQj2Qn2DJRZ8DKAvjXNQmo/tbweh
l+RGgbFge035kxDZ/t5pFweR/SYowAMdG2yOwA==

`pragma protect key_keyowner="ATRENTA", key_keyname="ATR-SG-2015-RSA-3", key_method="rsa"
`pragma protect encoding = (enctype="BASE64", line_length=76, bytes=256)
`pragma protect key_block
absLoVdCG0/WeiZ9M4NtAUjz+XnLze4vahkoVw40DL65GHoB/ikdBh+LyLQ7V3LckxaJp7Ihe1ow
2yXZZfuygvynBc+n/CI1EDwjo64cUTgVLg6gqySahs3D5Xkp8kFBBxARQmdoErJqqhefej6SXrxx
13OxNfq4vRGx7YG4l2M61gUhVtUX9poQdq5dxitmrLXD1kpdnUsj/YIpVBaLv/TBn9G44WiyRNIK
ojx9q2JyYKiWBfcBh+fpJV9PudrBUPMu8kvWsRizFr+r8Ya09D3o9iJUZ6FWOBiFsidvZNgmp1u/
nv56cp+qpaTesLtwmKiZbrhQtq6YXQvzPpDQXQ==

`pragma protect key_keyowner="Mentor Graphics Corporation", key_keyname="MGC-VELOCE-RSA", key_method="rsa"
`pragma protect encoding = (enctype="BASE64", line_length=76, bytes=128)
`pragma protect key_block
t2oJ825g01R4DfbjT3g+VDPmL9PAyVC2t8Ozl94Xb2xucD77bNiPcvutyZFkA0lqWfRMp8Z3kkTE
OOo/FpGS3c1SP04/jMKLZD9E7DL6iVBRfxa3itPHxsSD0RAP4yPHw3yCiIsmB0q25x8+so3h/QOv
DKZh98m5ku9UnG+pY6c=

`pragma protect key_keyowner="Mentor Graphics Corporation", key_keyname="MGC-VERIF-SIM-RSA-2", key_method="rsa"
`pragma protect encoding = (enctype="BASE64", line_length=76, bytes=256)
`pragma protect key_block
koDeaCPE+GNu9rMKu+nnX8UvNKbOa7mKCRwRUXCmZNo0yL7JuxnKQiStr89+6Ws9bOIbY8P6XKLC
WoSokcQl2MIZuh7gUJ+LQSPTB9HIkHPuGGPibAaiYY3e/6TBvv0+QG5gTvuf18Nz0UQyxRzNBFY7
2e0fNw+zoh4XJubbVaqqBBqTNyIM/naqx2G+DBhvJF/RlcpsJUe2eVt+uttis5ukRD1ndenp7rvA
+Ub6MDtoxunfFJsXEQ8QZkuZiT5XfcmJdkquGywSafJqKksYNJZpGleQnak/ePqKq8cYIbfpqOo1
MlqTFX2khe/WU/cqsW+5jXmRAgWueTOvg5hW2A==

`pragma protect key_keyowner="Real Intent", key_keyname="RI-RSA-KEY-1", key_method="rsa"
`pragma protect encoding = (enctype="BASE64", line_length=76, bytes=256)
`pragma protect key_block
wZaMVki09KtetQFaQKbOEpc8bkgxHSc8zyuzh+dwZ44uN2hbx3K7ITnC8dDkn3EMZGwk7C0u4eBt
eru14n5jQ1LfuUg4cKuwRNAgFxc7GaymqPYSRK9OQZHWZ+w6Alh4X9YWb6UVcsv4sCJA8YT9QeZ2
8PJYA3L+OY2t8Dcx3JcdLeVgMWDrP/zfpXyfMdPpwgBSSCqJHFsYdlG06onoQq2DDJ/SpC0W2oHU
JJAOTss7Cf3giWx2XTrorU5k4KbClTaEv4QAsogatkMf+oa9OfJQg5b7OUNbNqSzTV2IvRXtKIBC
N3mFkAtau93JXZzbow8bF+Y708RmUyIR5AX9og==

`pragma protect key_keyowner="Xilinx", key_keyname="xilinxt_2020_08", key_method="rsa"
`pragma protect encoding = (enctype="BASE64", line_length=76, bytes=256)
`pragma protect key_block
gidhQdKtgCKZpycO58SKONz/x64JxoYiDvm7CY7FhAgR8N3zqVR49qh/d9ImLGjAjXhz9ISSvhiE
1TpzIsqbVIoSEHhHCsw8fW3eNfjSKG9+5c0qMghoZBwnf9txWcso6wczPV8wSYfFgOnId+/H4w2u
MtSdrp2j2HeGCN7hmduXDeRIcLF+ekxNNZVk0wscD3yxYdFDWscebLgM1N+Cx8uwWvloVVe1fNSl
IBecuxue/tBnCdqw10D1fC8gGorhdNUhO2bTYqZL/+voIIAXkux7Z0BGx6B2uSJYuZ0j2LS23yyk
r0QDrL3YOpbEPBbFhTy9LQz59rkITBRhVeBqVg==

`pragma protect key_keyowner="Metrics Technologies Inc.", key_keyname="DSim", key_method="rsa"
`pragma protect encoding = (enctype="BASE64", line_length=76, bytes=256)
`pragma protect key_block
Lv7TtlI9EkMH+4ifu40NSGcF5VLP+fQr0uBXzvHjgpvggoEPEBlbTyXFtewlIbLNuHO4GjqSxFa3
oGjcKGgjJ4JKEHh9NZ/42sDCCnN1TS1zrfhPhpg3aJ3aGsOq5GxB6oAuNGvsTC7HgKk9lvgZfAiC
9ubfhd8fCUCrbS2jYuGLkpNxtwRxEbxLfMa6l2yusSJt8g6sfH0aGGBJWZjKnUZ1SyA1DmzZW3ox
o1AE17uwesEX5+JGPaqlsN+jLpbHhpv24GF4NS806LjJrXOO9qXbZScc78Z/R2xMBhLYAC0AHR8o
o8hlz9kYq3NSGSCdEMOcxNjVxDMYBrdZ+Lc+ag==

`pragma protect data_method = "AES128-CBC"
`pragma protect encoding = (enctype = "BASE64", line_length = 76, bytes = 2592)
`pragma protect data_block
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
UTw6QNma1ZQmEY+Uw72A+d8eTbRP3jDWseLm
`pragma protect end_protected
`pragma protect begin_protected
`pragma protect version = 1
`pragma protect encrypt_agent = "XILINX"
`pragma protect encrypt_agent_info = "Xilinx Encryption Tool 2020.2"
`pragma protect key_keyowner="Cadence Design Systems.", key_keyname="cds_rsa_key", key_method="rsa"
`pragma protect encoding = (enctype="BASE64", line_length=76, bytes=64)
`pragma protect key_block
R+TTV2BAhe9Ek8IveLCAIK+vyB2qa4TorazWyGCbrxCKkVhTBvAD6RqPeP/JqtRuh2zDPzraR9rT
gUyNSWD83A==

`pragma protect key_keyowner="Synopsys", key_keyname="SNPS-VCS-RSA-2", key_method="rsa"
`pragma protect encoding = (enctype="BASE64", line_length=76, bytes=128)
`pragma protect key_block
XM2mYTm+gCT0AhW4S5p7IlzH34WHm/fa2tLSENK5xQp44huwLBqk+dBcYbe4GM+6wqA3pzoUNE9T
SluI3P6DpsOt14ispiaJSciB+VdlU+Q0e63sKyfq++TGO3CTW5OhLIxojUbYrTbdY4WbGkk4yG0Y
qGwauBBx1uBueCA2GC4=

`pragma protect key_keyowner="Aldec", key_keyname="ALDEC15_001", key_method="rsa"
`pragma protect encoding = (enctype="BASE64", line_length=76, bytes=256)
`pragma protect key_block
M9U+BjMD5E96pT2zTDB1OSiHn8IS+G+aDNa3MIF/jeClLSPAOJwufjuzRcyAtwx0354Pb7AaFOwR
6CcoWPQM1dcUC6avyG/0PRrtZP/KpXS3/9PiWsaFHPYVLfqBMCUDoraXwfpfMxmOy8hD0iI6TtWc
j1xJUXVsbv+kqOeTUloYmwdRx/8cs46FvZfnFpiZXMFMsTsT9zvmCyNxiZefgFKT064BWsCkg2fa
W2IXperFJQzpE9mXVwGSjl6xDUp55esPyEPcDI4xy0T+q2KtBQj2Qn2DJRZ8DKAvjXNQmo/tbweh
l+RGgbFge035kxDZ/t5pFweR/SYowAMdG2yOwA==

`pragma protect key_keyowner="ATRENTA", key_keyname="ATR-SG-2015-RSA-3", key_method="rsa"
`pragma protect encoding = (enctype="BASE64", line_length=76, bytes=256)
`pragma protect key_block
absLoVdCG0/WeiZ9M4NtAUjz+XnLze4vahkoVw40DL65GHoB/ikdBh+LyLQ7V3LckxaJp7Ihe1ow
2yXZZfuygvynBc+n/CI1EDwjo64cUTgVLg6gqySahs3D5Xkp8kFBBxARQmdoErJqqhefej6SXrxx
13OxNfq4vRGx7YG4l2M61gUhVtUX9poQdq5dxitmrLXD1kpdnUsj/YIpVBaLv/TBn9G44WiyRNIK
ojx9q2JyYKiWBfcBh+fpJV9PudrBUPMu8kvWsRizFr+r8Ya09D3o9iJUZ6FWOBiFsidvZNgmp1u/
nv56cp+qpaTesLtwmKiZbrhQtq6YXQvzPpDQXQ==

`pragma protect key_keyowner="Mentor Graphics Corporation", key_keyname="MGC-VELOCE-RSA", key_method="rsa"
`pragma protect encoding = (enctype="BASE64", line_length=76, bytes=128)
`pragma protect key_block
t2oJ825g01R4DfbjT3g+VDPmL9PAyVC2t8Ozl94Xb2xucD77bNiPcvutyZFkA0lqWfRMp8Z3kkTE
OOo/FpGS3c1SP04/jMKLZD9E7DL6iVBRfxa3itPHxsSD0RAP4yPHw3yCiIsmB0q25x8+so3h/QOv
DKZh98m5ku9UnG+pY6c=

`pragma protect key_keyowner="Mentor Graphics Corporation", key_keyname="MGC-VERIF-SIM-RSA-2", key_method="rsa"
`pragma protect encoding = (enctype="BASE64", line_length=76, bytes=256)
`pragma protect key_block
koDeaCPE+GNu9rMKu+nnX8UvNKbOa7mKCRwRUXCmZNo0yL7JuxnKQiStr89+6Ws9bOIbY8P6XKLC
WoSokcQl2MIZuh7gUJ+LQSPTB9HIkHPuGGPibAaiYY3e/6TBvv0+QG5gTvuf18Nz0UQyxRzNBFY7
2e0fNw+zoh4XJubbVaqqBBqTNyIM/naqx2G+DBhvJF/RlcpsJUe2eVt+uttis5ukRD1ndenp7rvA
+Ub6MDtoxunfFJsXEQ8QZkuZiT5XfcmJdkquGywSafJqKksYNJZpGleQnak/ePqKq8cYIbfpqOo1
MlqTFX2khe/WU/cqsW+5jXmRAgWueTOvg5hW2A==

`pragma protect key_keyowner="Real Intent", key_keyname="RI-RSA-KEY-1", key_method="rsa"
`pragma protect encoding = (enctype="BASE64", line_length=76, bytes=256)
`pragma protect key_block
wZaMVki09KtetQFaQKbOEpc8bkgxHSc8zyuzh+dwZ44uN2hbx3K7ITnC8dDkn3EMZGwk7C0u4eBt
eru14n5jQ1LfuUg4cKuwRNAgFxc7GaymqPYSRK9OQZHWZ+w6Alh4X9YWb6UVcsv4sCJA8YT9QeZ2
8PJYA3L+OY2t8Dcx3JcdLeVgMWDrP/zfpXyfMdPpwgBSSCqJHFsYdlG06onoQq2DDJ/SpC0W2oHU
JJAOTss7Cf3giWx2XTrorU5k4KbClTaEv4QAsogatkMf+oa9OfJQg5b7OUNbNqSzTV2IvRXtKIBC
N3mFkAtau93JXZzbow8bF+Y708RmUyIR5AX9og==

`pragma protect key_keyowner="Xilinx", key_keyname="xilinxt_2020_08", key_method="rsa"
`pragma protect encoding = (enctype="BASE64", line_length=76, bytes=256)
`pragma protect key_block
gidhQdKtgCKZpycO58SKONz/x64JxoYiDvm7CY7FhAgR8N3zqVR49qh/d9ImLGjAjXhz9ISSvhiE
1TpzIsqbVIoSEHhHCsw8fW3eNfjSKG9+5c0qMghoZBwnf9txWcso6wczPV8wSYfFgOnId+/H4w2u
MtSdrp2j2HeGCN7hmduXDeRIcLF+ekxNNZVk0wscD3yxYdFDWscebLgM1N+Cx8uwWvloVVe1fNSl
IBecuxue/tBnCdqw10D1fC8gGorhdNUhO2bTYqZL/+voIIAXkux7Z0BGx6B2uSJYuZ0j2LS23yyk
r0QDrL3YOpbEPBbFhTy9LQz59rkITBRhVeBqVg==

`pragma protect key_keyowner="Metrics Technologies Inc.", key_keyname="DSim", key_method="rsa"
`pragma protect encoding = (enctype="BASE64", line_length=76, bytes=256)
`pragma protect key_block
Lv7TtlI9EkMH+4ifu40NSGcF5VLP+fQr0uBXzvHjgpvggoEPEBlbTyXFtewlIbLNuHO4GjqSxFa3
oGjcKGgjJ4JKEHh9NZ/42sDCCnN1TS1zrfhPhpg3aJ3aGsOq5GxB6oAuNGvsTC7HgKk9lvgZfAiC
9ubfhd8fCUCrbS2jYuGLkpNxtwRxEbxLfMa6l2yusSJt8g6sfH0aGGBJWZjKnUZ1SyA1DmzZW3ox
o1AE17uwesEX5+JGPaqlsN+jLpbHhpv24GF4NS806LjJrXOO9qXbZScc78Z/R2xMBhLYAC0AHR8o
o8hlz9kYq3NSGSCdEMOcxNjVxDMYBrdZ+Lc+ag==

`pragma protect key_keyowner="Mentor Graphics Corporation", key_keyname="MGC-PREC-RSA", key_method="rsa"
`pragma protect encoding = (enctype="BASE64", line_length=76, bytes=256)
`pragma protect key_block
gPP4NKH4BqgmS2ygf4ca8YwE4BHuXIDyWG/GpU+oRN5O+BkQ8SrVivRffvrKWrMfu6GkvqMtUMSC
COf0P+HFZg7iKu2/RqMBtiw5io29wBKGTLwDtx0DHKHACdQoza3qEJyPYhi4tBG11fAM4YlJ33QS
2tUq6zMBn+1mC2UU3By3KR2oYF/6UB22Rz1unpf71e+dsZN2NKy0VXCmWhA24qPv7V01n6+XfAcC
TyA8wAscsINTiP3/og8icYE5sA6F0CSfRSCO3MjM3QWHXvArX8X0Jis53gt+R+N1cIfWIq8emnP3
bSqEQ+v72oxfxfy2K4i2BBpx4lIoUCycWH0M5Q==

`pragma protect key_keyowner="Synplicity", key_keyname="SYNP15_1", key_method="rsa"
`pragma protect encoding = (enctype="BASE64", line_length=76, bytes=256)
`pragma protect key_block
oiqMBPSOuR4owMU2RNDPJdEf/hF9qK03rWZWjMYIrX2pT50NTiDFsXA/CodOWUoq8k1sNlpi8QfT
1vYwbQesqTdDvreW2acN2I/vu3yLFYEME/q6WFmSF0LemAVWUw8NNkeFs1CjPSrot9xqK40NXmTY
fViAgq9rDJ1bwZLkG6g4HFyjSCMQf6GxV76+jLE1XPH/881Hribi+wi/ghKbuZgJAHgG7GmePyb+
FGWRGLTsapoqC+9ZQZXRph8JzKGpNCUC+ZSZpId7GlEVqXQKVa1K2tx03BUkzlTWA7PU5nO6WORY
HjCX4bs7HxtVA+LR79d0J19RA22UMUtC+ALbeA==

`pragma protect data_method = "AES128-CBC"
`pragma protect encoding = (enctype = "BASE64", line_length = 76, bytes = 11520)
`pragma protect data_block
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
MmOI/wgM
`pragma protect end_protected
`ifndef GLBL
`define GLBL
`timescale  1 ps / 1 ps

module glbl ();

    parameter ROC_WIDTH = 100000;
    parameter TOC_WIDTH = 0;
    parameter GRES_WIDTH = 10000;
    parameter GRES_START = 10000;

//--------   STARTUP Globals --------------
    wire GSR;
    wire GTS;
    wire GWE;
    wire PRLD;
    wire GRESTORE;
    tri1 p_up_tmp;
    tri (weak1, strong0) PLL_LOCKG = p_up_tmp;

    wire PROGB_GLBL;
    wire CCLKO_GLBL;
    wire FCSBO_GLBL;
    wire [3:0] DO_GLBL;
    wire [3:0] DI_GLBL;
   
    reg GSR_int;
    reg GTS_int;
    reg PRLD_int;
    reg GRESTORE_int;

//--------   JTAG Globals --------------
    wire JTAG_TDO_GLBL;
    wire JTAG_TCK_GLBL;
    wire JTAG_TDI_GLBL;
    wire JTAG_TMS_GLBL;
    wire JTAG_TRST_GLBL;

    reg JTAG_CAPTURE_GLBL;
    reg JTAG_RESET_GLBL;
    reg JTAG_SHIFT_GLBL;
    reg JTAG_UPDATE_GLBL;
    reg JTAG_RUNTEST_GLBL;

    reg JTAG_SEL1_GLBL = 0;
    reg JTAG_SEL2_GLBL = 0 ;
    reg JTAG_SEL3_GLBL = 0;
    reg JTAG_SEL4_GLBL = 0;

    reg JTAG_USER_TDO1_GLBL = 1'bz;
    reg JTAG_USER_TDO2_GLBL = 1'bz;
    reg JTAG_USER_TDO3_GLBL = 1'bz;
    reg JTAG_USER_TDO4_GLBL = 1'bz;

    assign (strong1, weak0) GSR = GSR_int;
    assign (strong1, weak0) GTS = GTS_int;
    assign (weak1, weak0) PRLD = PRLD_int;
    assign (strong1, weak0) GRESTORE = GRESTORE_int;

    initial begin
	GSR_int = 1'b1;
	PRLD_int = 1'b1;
	#(ROC_WIDTH)
	GSR_int = 1'b0;
	PRLD_int = 1'b0;
    end

    initial begin
	GTS_int = 1'b1;
	#(TOC_WIDTH)
	GTS_int = 1'b0;
    end

    initial begin 
	GRESTORE_int = 1'b0;
	#(GRES_START);
	GRESTORE_int = 1'b1;
	#(GRES_WIDTH);
	GRESTORE_int = 1'b0;
    end

endmodule
`endif
