simonyiszk/open-hf-sdr/vivado/ha5kfu_ws2/ha5kfu_ws2.srcs/sources_1/bd/top/ip/top_c_addsub_0_0/top_c_addsub_0_0_sim_netlist.vhdl

-- Copyright 1986-2020 Xilinx, Inc. All Rights Reserved.
-- --------------------------------------------------------------------------------
-- Tool Version: Vivado v.2020.2 (win64) Build 3064766 Wed Nov 18 09:12:45 MST 2020
-- Date        : Fri Feb 12 23:06:55 2021
-- Host        : RemoteApp running 64-bit major release  (build 9200)
-- Command     : write_vhdl -force -mode funcsim -rename_top top_c_addsub_0_0 -prefix
--               top_c_addsub_0_0_ top_c_addsub_0_0_sim_netlist.vhdl
-- Design      : top_c_addsub_0_0
-- Purpose     : This VHDL netlist is a functional simulation representation of the design and should not be modified or
--               synthesized. This netlist cannot be used for SDF annotated simulation.
-- Device      : xc7s6ftgb196-1
-- --------------------------------------------------------------------------------
`protect begin_protected
`protect version = 1
`protect encrypt_agent = "XILINX"
`protect encrypt_agent_info = "Xilinx Encryption Tool 2020.2"
`protect key_keyowner="Cadence Design Systems.", key_keyname="cds_rsa_key", key_method="rsa"
`protect encoding = (enctype="BASE64", line_length=76, bytes=64)
`protect key_block
nwI9apodsxWnt8/qZ84l2L5r2ru1rYRvzH+cIiU2LZ7ZFrYGVhrKUku8GacxvPmk04mNLHGAUf3D
0KN1yrZ0UA==

`protect key_keyowner="Synopsys", key_keyname="SNPS-VCS-RSA-2", key_method="rsa"
`protect encoding = (enctype="BASE64", line_length=76, bytes=128)
`protect key_block
Sm1hR/bXnEX5hSLJC+m0q+qTo+GE1jW/bGh9GYODVR1B61WO0x3DI91rmMkLB3jXabqZYmZaVRnk
N8AiDf+w3tD5cTm9k3UfnHfkmqEgj8LBJAWCYHciLWzjmW7DKTQG5Copg5YaoAmLrkH/R11p2QBq
US3uTE+2f5z8QlQwimE=

`protect key_keyowner="Aldec", key_keyname="ALDEC15_001", key_method="rsa"
`protect encoding = (enctype="BASE64", line_length=76, bytes=256)
`protect key_block
y/EngzI5VWuiEHV+TKhmZG2qH1QkzhsLqS3InhpMlNY6l/FsFenjJYgIcwfRB5cHNIe7FLSQt6Ne
y3HMmpsqF6xetN1AMKtt7yIa7k99d/5TC5vyU4dMYs9g27cqHYJzk93esgZCvjIZLHpcXw/tu9/b
4U5FbTjst4GUWQQ7e+FOVWa1BC4H7jo6ZOE8mZ1oMeTUDMRBFFBQWv4xUZFg+dKul2euXKFScShR
h6tknaycBcdNbA+6dQJo+VgrTTewvfrkpNyifPBwk9vIitRhFkJJJVGsR6T+AF/UJfY5dEYYFuu5
J288ggKjbjEUNQnIyNWOpZiuhpClTTay3laNkw==

`protect key_keyowner="ATRENTA", key_keyname="ATR-SG-2015-RSA-3", key_method="rsa"
`protect encoding = (enctype="BASE64", line_length=76, bytes=256)
`protect key_block
htKUMvAlzdN4BbAAeNmEM6Yr1UUCORwvd6+1cV737AnX/e5QyMGFY1ZuaVzrrzfIKK+VWd/bFDYR
WeL3jKvGUsyl0cMQ9jcxLrsCI3RnUD8yDbbqyDu9KMj34D7UA/k879CbEg7mJQsE/OUuwmk5Rusa
S2E+UVp+HrYNnNymuLmmn6wOTCKRZjZEMW81xyRvJrDTTqf12SjMprM/ubdETBwwiEzoIwLeibWv
EE77NEiYVwYpzXElBkB+JN+riXCrervjpMbAzHbeomW24pwXmffMMvkj1nRzaEI2QRT19Hpc4iqq
tT7PSLFxC6iyyFn2bd5a57kSCEK5ZaaxszxEVg==

`protect key_keyowner="Mentor Graphics Corporation", key_keyname="MGC-VELOCE-RSA", key_method="rsa"
`protect encoding = (enctype="BASE64", line_length=76, bytes=128)
`protect key_block
ST+OORnrF+3QguD7AuqTgC907V9FPxT3xpP2TfPbwAQB2+m85/czQ7xrlMYLNRNl2qldRPC2JAtf
yRLJmvKEgyRtR6tv/9gg66CdnvMVGbBmprZnmsgKpHGXcIGIVm6FR+ifL/5pZcFZyTQCKYlbE6bz
YNrIQ8EskAk5YXNHRZU=

`protect key_keyowner="Mentor Graphics Corporation", key_keyname="MGC-VERIF-SIM-RSA-2", key_method="rsa"
`protect encoding = (enctype="BASE64", line_length=76, bytes=256)
`protect key_block
Zz8HkbKk2BMn9pYqHdEWEMFHnKjJed8tZnBzajqsks1G6q0CzbV0FSYoWS1nKj84tIU1JkBaGDIt
9sdF4TFidxOJyhtrmpNfTChKxpMr41K8vo0yCOwdi29v/VShuI/rkIBCSgrdlmTBWBEgiBS9aabp
Jqqjo1ol263k6jlcp9rOjaoU+lcQMEXCkHoZu/V2+VWtTqhoSiWKgDQ0jJptGQig3wemEM16ctGQ
xX4urrzlEYCVTlr9g3mn6x8NgAjEFjJqmg1uE21AWGXfsNowkj2dYZLCXuVTF108ULXlOgx8TBHk
tPYc56T7eylPXV3Y05Z7agtvOLTYldGNSnm7qQ==

`protect key_keyowner="Real Intent", key_keyname="RI-RSA-KEY-1", key_method="rsa"
`protect encoding = (enctype="BASE64", line_length=76, bytes=256)
`protect key_block
VHzNHo3jyVixjpbjlcbNuO7IrIjCuYoXTAjRb06/SIYnbUS1pXATLQwryf5S2ETq0CYvThlIAGS0
xbNOLpEIhHMaY4VNrUdhUPBHXcXHWUCHudYKaUCB/Pk28QZKLuHYt3FqZh6wdzI6AFJdP/pykVJb
M/Pyyc+uLtqsAqyWqtJ0puNrBSpFPSM5259v7Gum4dwYGluRNUyJPq0CnQOQDcjaKw42cmf2DAtX
CSJb79mvoLdsFiW5ePQbcfrrcT/FhIkNj4/DqMVl2EB85zQgcPJw5Up3lLGw0Qd2Cd1jeq3A4qcf
LraHhfdfhy6tS33yDqFUeXlzvLfkicvxivScIw==

`protect key_keyowner="Xilinx", key_keyname="xilinxt_2020_08", key_method="rsa"
`protect encoding = (enctype="BASE64", line_length=76, bytes=256)
`protect key_block
Ir7vg+6icGbLB3CLLO2WEVH7p5OyaYzRs27g9ktjlLGEA8UZWJVD/LEebYJEdrotzhB8SWmHZMDV
/tU66bmEBeBvDhzPDFffP8JEne90WI2d4WsOz8gc/qUmQrWkWWpKaGeRzRKobk6HEaC+nXg3PqfM
0b03fbE0S205+4xE/rEnuHBIRBfZd3xmeVaB0HKBt0SGPD5SSQQZpPD38QOtCELjuuuA4RtmpS90
kaKEHc7Je6wpd85YQOJtbSfSfwms8QmBrV2vuYX5vgvFoWdrKhFu6ei5xOtYRK3gX3JKdEXLebbV
49uISo0iQ96Wfdc+51UDQD4Z2sSmPF/BKuQ5nQ==

`protect key_keyowner="Metrics Technologies Inc.", key_keyname="DSim", key_method="rsa"
`protect encoding = (enctype="BASE64", line_length=76, bytes=256)
`protect key_block
LpdRmMYH4gdKs52wqPlK6TsP8t36Rz9etYG+uFXIxoYPOw77GvCpHTnPEq4wgKvtHfjSBYM58T8o
VFR+rx+dgG80Vv61h2/ALXu7WMVNRnj432YN7jUfiNGlmdGjYf7j5bb6jDSZd9SGg9hOG322ua8w
FL0iNhZ1+8bqOC5DHZhVoYhtH7wentMTqEBB4I+Xy3zK2H07hbY20A+hZ5iviyCzHMtmQ5LCJzAb
8LeBnGRdOv8ntIJz3n1voQKFpamiYGRWqDwIHC+A3vf0VlEiw8M53hPC9SjoIQqQxSnkzTditbkH
fDStRcfPfMIOJ9yoREe7QoWlh0XCwpflnMvnNg==

`protect key_keyowner="Mentor Graphics Corporation", key_keyname="MGC-PREC-RSA", key_method="rsa"
`protect encoding = (enctype="BASE64", line_length=76, bytes=256)
`protect key_block
okOOc/WZujDBaKHoRojtNmZx7bCQ7QiXurkY3Pq2ZmxxaUKkvPadVQatTuYGXvdoV6ezvuJrYW1g
fmOXFggi7zRp6tQMoJQa1dTCuxW1nCEmSTltJHPvqEW/RZHsQ/0QOzU+QrPCvYxsdVk33knV92Ql
iWcazGMRTbKF+k9osjnCL/HskkELV6g1sw7q5h0Whl+mJRSUGklEzkT1FoRku9qMOyIh6aUTsVLk
cygVmDA57cBbNW+ih+NELEyOFTY4d4BsuOGWtzOLWgzoU2bp8CXMHXLI4QfvH4OY5bog4x7WGVVL
WdbsE46M40BTKD9C5nP2pR0xgqDjLhlaPYCRGg==

`protect key_keyowner="Synplicity", key_keyname="SYNP15_1", key_method="rsa"
`protect encoding = (enctype="BASE64", line_length=76, bytes=256)
`protect key_block
mZEGA62i3Fa/844PCIwrghoNI0aPLy9GhRS9TDeype31whyE+QcbfEu26aNwkqp7oFHl89sejVx2
tbjAg3LWRpV1Ow/sWrbvQol38djYLGTV0m9GvdeWjTgkN+s7tUNxA7V4topEjToWtEkYbt1K4qg/
bK3EQDyeSiKwc4e/nCubBKnZMzHp+blCctkE7Jd1QBjZiOI0cobVCAWxCclVWJb3iviylVlNgxCf
bXW/UNK7tPZx3I/Lp/NzeiO3bm5Ll3ZMsj6JLp8DRtRSMd1sfXeKHGUCM0FdgaYtxzHzHwoLbZAA
QbOS0ia7EicfUMEIqQYzk02hUzCuQepuhhGcSQ==

`protect data_method = "AES128-CBC"
`protect encoding = (enctype = "BASE64", line_length = 76, bytes = 19680)
`protect data_block
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
KIhmcrp1ru4WbDNwT6v7
`protect end_protected
`protect begin_protected
`protect version = 1
`protect encrypt_agent = "XILINX"
`protect encrypt_agent_info = "Xilinx Encryption Tool 2020.2"
`protect key_keyowner="Cadence Design Systems.", key_keyname="cds_rsa_key", key_method="rsa"
`protect encoding = (enctype="BASE64", line_length=76, bytes=64)
`protect key_block
R+TTV2BAhe9Ek8IveLCAIK+vyB2qa4TorazWyGCbrxCKkVhTBvAD6RqPeP/JqtRuh2zDPzraR9rT
gUyNSWD83A==

`protect key_keyowner="Synopsys", key_keyname="SNPS-VCS-RSA-2", key_method="rsa"
`protect encoding = (enctype="BASE64", line_length=76, bytes=128)
`protect key_block
XM2mYTm+gCT0AhW4S5p7IlzH34WHm/fa2tLSENK5xQp44huwLBqk+dBcYbe4GM+6wqA3pzoUNE9T
SluI3P6DpsOt14ispiaJSciB+VdlU+Q0e63sKyfq++TGO3CTW5OhLIxojUbYrTbdY4WbGkk4yG0Y
qGwauBBx1uBueCA2GC4=

`protect key_keyowner="Aldec", key_keyname="ALDEC15_001", key_method="rsa"
`protect encoding = (enctype="BASE64", line_length=76, bytes=256)
`protect key_block
M9U+BjMD5E96pT2zTDB1OSiHn8IS+G+aDNa3MIF/jeClLSPAOJwufjuzRcyAtwx0354Pb7AaFOwR
6CcoWPQM1dcUC6avyG/0PRrtZP/KpXS3/9PiWsaFHPYVLfqBMCUDoraXwfpfMxmOy8hD0iI6TtWc
j1xJUXVsbv+kqOeTUloYmwdRx/8cs46FvZfnFpiZXMFMsTsT9zvmCyNxiZefgFKT064BWsCkg2fa
W2IXperFJQzpE9mXVwGSjl6xDUp55esPyEPcDI4xy0T+q2KtBQj2Qn2DJRZ8DKAvjXNQmo/tbweh
l+RGgbFge035kxDZ/t5pFweR/SYowAMdG2yOwA==

`protect key_keyowner="ATRENTA", key_keyname="ATR-SG-2015-RSA-3", key_method="rsa"
`protect encoding = (enctype="BASE64", line_length=76, bytes=256)
`protect key_block
absLoVdCG0/WeiZ9M4NtAUjz+XnLze4vahkoVw40DL65GHoB/ikdBh+LyLQ7V3LckxaJp7Ihe1ow
2yXZZfuygvynBc+n/CI1EDwjo64cUTgVLg6gqySahs3D5Xkp8kFBBxARQmdoErJqqhefej6SXrxx
13OxNfq4vRGx7YG4l2M61gUhVtUX9poQdq5dxitmrLXD1kpdnUsj/YIpVBaLv/TBn9G44WiyRNIK
ojx9q2JyYKiWBfcBh+fpJV9PudrBUPMu8kvWsRizFr+r8Ya09D3o9iJUZ6FWOBiFsidvZNgmp1u/
nv56cp+qpaTesLtwmKiZbrhQtq6YXQvzPpDQXQ==

`protect key_keyowner="Mentor Graphics Corporation", key_keyname="MGC-VELOCE-RSA", key_method="rsa"
`protect encoding = (enctype="BASE64", line_length=76, bytes=128)
`protect key_block
t2oJ825g01R4DfbjT3g+VDPmL9PAyVC2t8Ozl94Xb2xucD77bNiPcvutyZFkA0lqWfRMp8Z3kkTE
OOo/FpGS3c1SP04/jMKLZD9E7DL6iVBRfxa3itPHxsSD0RAP4yPHw3yCiIsmB0q25x8+so3h/QOv
DKZh98m5ku9UnG+pY6c=

`protect key_keyowner="Mentor Graphics Corporation", key_keyname="MGC-VERIF-SIM-RSA-2", key_method="rsa"
`protect encoding = (enctype="BASE64", line_length=76, bytes=256)
`protect key_block
koDeaCPE+GNu9rMKu+nnX8UvNKbOa7mKCRwRUXCmZNo0yL7JuxnKQiStr89+6Ws9bOIbY8P6XKLC
WoSokcQl2MIZuh7gUJ+LQSPTB9HIkHPuGGPibAaiYY3e/6TBvv0+QG5gTvuf18Nz0UQyxRzNBFY7
2e0fNw+zoh4XJubbVaqqBBqTNyIM/naqx2G+DBhvJF/RlcpsJUe2eVt+uttis5ukRD1ndenp7rvA
+Ub6MDtoxunfFJsXEQ8QZkuZiT5XfcmJdkquGywSafJqKksYNJZpGleQnak/ePqKq8cYIbfpqOo1
MlqTFX2khe/WU/cqsW+5jXmRAgWueTOvg5hW2A==

`protect key_keyowner="Real Intent", key_keyname="RI-RSA-KEY-1", key_method="rsa"
`protect encoding = (enctype="BASE64", line_length=76, bytes=256)
`protect key_block
wZaMVki09KtetQFaQKbOEpc8bkgxHSc8zyuzh+dwZ44uN2hbx3K7ITnC8dDkn3EMZGwk7C0u4eBt
eru14n5jQ1LfuUg4cKuwRNAgFxc7GaymqPYSRK9OQZHWZ+w6Alh4X9YWb6UVcsv4sCJA8YT9QeZ2
8PJYA3L+OY2t8Dcx3JcdLeVgMWDrP/zfpXyfMdPpwgBSSCqJHFsYdlG06onoQq2DDJ/SpC0W2oHU
JJAOTss7Cf3giWx2XTrorU5k4KbClTaEv4QAsogatkMf+oa9OfJQg5b7OUNbNqSzTV2IvRXtKIBC
N3mFkAtau93JXZzbow8bF+Y708RmUyIR5AX9og==

`protect key_keyowner="Xilinx", key_keyname="xilinxt_2020_08", key_method="rsa"
`protect encoding = (enctype="BASE64", line_length=76, bytes=256)
`protect key_block
gidhQdKtgCKZpycO58SKONz/x64JxoYiDvm7CY7FhAgR8N3zqVR49qh/d9ImLGjAjXhz9ISSvhiE
1TpzIsqbVIoSEHhHCsw8fW3eNfjSKG9+5c0qMghoZBwnf9txWcso6wczPV8wSYfFgOnId+/H4w2u
MtSdrp2j2HeGCN7hmduXDeRIcLF+ekxNNZVk0wscD3yxYdFDWscebLgM1N+Cx8uwWvloVVe1fNSl
IBecuxue/tBnCdqw10D1fC8gGorhdNUhO2bTYqZL/+voIIAXkux7Z0BGx6B2uSJYuZ0j2LS23yyk
r0QDrL3YOpbEPBbFhTy9LQz59rkITBRhVeBqVg==

`protect key_keyowner="Metrics Technologies Inc.", key_keyname="DSim", key_method="rsa"
`protect encoding = (enctype="BASE64", line_length=76, bytes=256)
`protect key_block
Lv7TtlI9EkMH+4ifu40NSGcF5VLP+fQr0uBXzvHjgpvggoEPEBlbTyXFtewlIbLNuHO4GjqSxFa3
oGjcKGgjJ4JKEHh9NZ/42sDCCnN1TS1zrfhPhpg3aJ3aGsOq5GxB6oAuNGvsTC7HgKk9lvgZfAiC
9ubfhd8fCUCrbS2jYuGLkpNxtwRxEbxLfMa6l2yusSJt8g6sfH0aGGBJWZjKnUZ1SyA1DmzZW3ox
o1AE17uwesEX5+JGPaqlsN+jLpbHhpv24GF4NS806LjJrXOO9qXbZScc78Z/R2xMBhLYAC0AHR8o
o8hlz9kYq3NSGSCdEMOcxNjVxDMYBrdZ+Lc+ag==

`protect data_method = "AES128-CBC"
`protect encoding = (enctype = "BASE64", line_length = 76, bytes = 6432)
`protect data_block
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
`protect end_protected
library IEEE;
use IEEE.STD_LOGIC_1164.ALL;
library UNISIM;
use UNISIM.VCOMPONENTS.ALL;
entity top_c_addsub_0_0 is
  port (
    A : in STD_LOGIC_VECTOR ( 12 downto 0 );
    B : in STD_LOGIC_VECTOR ( 12 downto 0 );
    CLK : in STD_LOGIC;
    S : out STD_LOGIC_VECTOR ( 13 downto 0 )
  );
  attribute NotValidForBitStream : boolean;
  attribute NotValidForBitStream of top_c_addsub_0_0 : entity is true;
  attribute CHECK_LICENSE_TYPE : string;
  attribute CHECK_LICENSE_TYPE of top_c_addsub_0_0 : entity is "top_c_addsub_0_0,c_addsub_v12_0_14,{}";
  attribute downgradeipidentifiedwarnings : string;
  attribute downgradeipidentifiedwarnings of top_c_addsub_0_0 : entity is "yes";
  attribute x_core_info : string;
  attribute x_core_info of top_c_addsub_0_0 : entity is "c_addsub_v12_0_14,Vivado 2020.2";
end top_c_addsub_0_0;

architecture STRUCTURE of top_c_addsub_0_0 is
  signal NLW_U0_C_OUT_UNCONNECTED : STD_LOGIC;
  attribute C_AINIT_VAL : string;
  attribute C_AINIT_VAL of U0 : label is "0";
  attribute C_BORROW_LOW : integer;
  attribute C_BORROW_LOW of U0 : label is 1;
  attribute C_CE_OVERRIDES_BYPASS : integer;
  attribute C_CE_OVERRIDES_BYPASS of U0 : label is 1;
  attribute C_CE_OVERRIDES_SCLR : integer;
  attribute C_CE_OVERRIDES_SCLR of U0 : label is 0;
  attribute C_HAS_CE : integer;
  attribute C_HAS_CE of U0 : label is 0;
  attribute C_HAS_SCLR : integer;
  attribute C_HAS_SCLR of U0 : label is 0;
  attribute C_HAS_SINIT : integer;
  attribute C_HAS_SINIT of U0 : label is 0;
  attribute C_HAS_SSET : integer;
  attribute C_HAS_SSET of U0 : label is 0;
  attribute C_IMPLEMENTATION : integer;
  attribute C_IMPLEMENTATION of U0 : label is 0;
  attribute C_SCLR_OVERRIDES_SSET : integer;
  attribute C_SCLR_OVERRIDES_SSET of U0 : label is 1;
  attribute C_SINIT_VAL : string;
  attribute C_SINIT_VAL of U0 : label is "0";
  attribute C_VERBOSITY : integer;
  attribute C_VERBOSITY of U0 : label is 0;
  attribute C_XDEVICEFAMILY : string;
  attribute C_XDEVICEFAMILY of U0 : label is "spartan7";
  attribute c_a_type : integer;
  attribute c_a_type of U0 : label is 0;
  attribute c_a_width : integer;
  attribute c_a_width of U0 : label is 13;
  attribute c_add_mode : integer;
  attribute c_add_mode of U0 : label is 0;
  attribute c_b_constant : integer;
  attribute c_b_constant of U0 : label is 0;
  attribute c_b_type : integer;
  attribute c_b_type of U0 : label is 0;
  attribute c_b_value : string;
  attribute c_b_value of U0 : label is "0000000000000";
  attribute c_b_width : integer;
  attribute c_b_width of U0 : label is 13;
  attribute c_bypass_low : integer;
  attribute c_bypass_low of U0 : label is 0;
  attribute c_has_bypass : integer;
  attribute c_has_bypass of U0 : label is 0;
  attribute c_has_c_in : integer;
  attribute c_has_c_in of U0 : label is 0;
  attribute c_has_c_out : integer;
  attribute c_has_c_out of U0 : label is 0;
  attribute c_latency : integer;
  attribute c_latency of U0 : label is 1;
  attribute c_out_width : integer;
  attribute c_out_width of U0 : label is 14;
  attribute downgradeipidentifiedwarnings of U0 : label is "yes";
  attribute is_du_within_envelope : string;
  attribute is_du_within_envelope of U0 : label is "true";
  attribute x_interface_info : string;
  attribute x_interface_info of CLK : signal is "xilinx.com:signal:clock:1.0 clk_intf CLK";
  attribute x_interface_parameter : string;
  attribute x_interface_parameter of CLK : signal is "XIL_INTERFACENAME clk_intf, ASSOCIATED_BUSIF s_intf:c_out_intf:sinit_intf:sset_intf:bypass_intf:c_in_intf:add_intf:b_intf:a_intf, ASSOCIATED_RESET SCLR, ASSOCIATED_CLKEN CE, FREQ_HZ 125000000, FREQ_TOLERANCE_HZ 0, PHASE 0.000, CLK_DOMAIN top_clk, INSERT_VIP 0";
  attribute x_interface_info of A : signal is "xilinx.com:signal:data:1.0 a_intf DATA";
  attribute x_interface_parameter of A : signal is "XIL_INTERFACENAME a_intf, LAYERED_METADATA xilinx.com:interface:datatypes:1.0 {DATA {datatype {name {attribs {resolve_type immediate dependency {} format string minimum {} maximum {}} value data} bitwidth {attribs {resolve_type generated dependency bitwidth format long minimum {} maximum {}} value 13} bitoffset {attribs {resolve_type immediate dependency {} format long minimum {} maximum {}} value 0} integer {signed {attribs {resolve_type generated dependency signed format bool minimum {} maximum {}} value TRUE}}}} DATA_WIDTH 13}";
  attribute x_interface_info of B : signal is "xilinx.com:signal:data:1.0 b_intf DATA";
  attribute x_interface_parameter of B : signal is "XIL_INTERFACENAME b_intf, LAYERED_METADATA xilinx.com:interface:datatypes:1.0 {DATA {datatype {name {attribs {resolve_type immediate dependency {} format string minimum {} maximum {}} value data} bitwidth {attribs {resolve_type generated dependency bitwidth format long minimum {} maximum {}} value 13} bitoffset {attribs {resolve_type immediate dependency {} format long minimum {} maximum {}} value 0} integer {signed {attribs {resolve_type generated dependency signed format bool minimum {} maximum {}} value TRUE}}}} DATA_WIDTH 13}";
  attribute x_interface_info of S : signal is "xilinx.com:signal:data:1.0 s_intf DATA";
  attribute x_interface_parameter of S : signal is "XIL_INTERFACENAME s_intf, LAYERED_METADATA xilinx.com:interface:datatypes:1.0 {DATA {datatype {name {attribs {resolve_type immediate dependency {} format string minimum {} maximum {}} value data} bitwidth {attribs {resolve_type generated dependency bitwidth format long minimum {} maximum {}} value 14} bitoffset {attribs {resolve_type immediate dependency {} format long minimum {} maximum {}} value 0} integer {signed {attribs {resolve_type generated dependency signed format bool minimum {} maximum {}} value TRUE}}}} DATA_WIDTH 14}";
begin
U0: entity work.top_c_addsub_0_0_c_addsub_v12_0_14
     port map (
      A(12 downto 0) => A(12 downto 0),
      ADD => '1',
      B(12 downto 0) => B(12 downto 0),
      BYPASS => '0',
      CE => '1',
      CLK => CLK,
      C_IN => '0',
      C_OUT => NLW_U0_C_OUT_UNCONNECTED,
      S(13 downto 0) => S(13 downto 0),
      SCLR => '0',
      SINIT => '0',
      SSET => '0'
    );
end STRUCTURE;
