simonyiszk/open-hf-sdr/vivado/ha5kfu_ws2/ha5kfu_ws2.srcs/sources_1/bd/top/ip/top_c_counter_binary_i_0/top_c_counter_binary_i_0_sim_netlist.vhdl

-- Copyright 1986-2020 Xilinx, Inc. All Rights Reserved.
-- --------------------------------------------------------------------------------
-- Tool Version: Vivado v.2020.2 (win64) Build 3064766 Wed Nov 18 09:12:45 MST 2020
-- Date        : Fri Feb 12 23:06:56 2021
-- Host        : RemoteApp running 64-bit major release  (build 9200)
-- Command     : write_vhdl -force -mode funcsim -rename_top top_c_counter_binary_i_0 -prefix
--               top_c_counter_binary_i_0_ top_c_counter_binary_i_0_sim_netlist.vhdl
-- Design      : top_c_counter_binary_i_0
-- Purpose     : This VHDL netlist is a functional simulation representation of the design and should not be modified or
--               synthesized. This netlist cannot be used for SDF annotated simulation.
-- Device      : xc7s6ftgb196-1
-- --------------------------------------------------------------------------------
`protect begin_protected
`protect version = 1
`protect encrypt_agent = "XILINX"
`protect encrypt_agent_info = "Xilinx Encryption Tool 2020.2"
`protect key_keyowner="Cadence Design Systems.", key_keyname="cds_rsa_key", key_method="rsa"
`protect encoding = (enctype="BASE64", line_length=76, bytes=64)
`protect key_block
nwI9apodsxWnt8/qZ84l2L5r2ru1rYRvzH+cIiU2LZ7ZFrYGVhrKUku8GacxvPmk04mNLHGAUf3D
0KN1yrZ0UA==

`protect key_keyowner="Synopsys", key_keyname="SNPS-VCS-RSA-2", key_method="rsa"
`protect encoding = (enctype="BASE64", line_length=76, bytes=128)
`protect key_block
Sm1hR/bXnEX5hSLJC+m0q+qTo+GE1jW/bGh9GYODVR1B61WO0x3DI91rmMkLB3jXabqZYmZaVRnk
N8AiDf+w3tD5cTm9k3UfnHfkmqEgj8LBJAWCYHciLWzjmW7DKTQG5Copg5YaoAmLrkH/R11p2QBq
US3uTE+2f5z8QlQwimE=

`protect key_keyowner="Aldec", key_keyname="ALDEC15_001", key_method="rsa"
`protect encoding = (enctype="BASE64", line_length=76, bytes=256)
`protect key_block
y/EngzI5VWuiEHV+TKhmZG2qH1QkzhsLqS3InhpMlNY6l/FsFenjJYgIcwfRB5cHNIe7FLSQt6Ne
y3HMmpsqF6xetN1AMKtt7yIa7k99d/5TC5vyU4dMYs9g27cqHYJzk93esgZCvjIZLHpcXw/tu9/b
4U5FbTjst4GUWQQ7e+FOVWa1BC4H7jo6ZOE8mZ1oMeTUDMRBFFBQWv4xUZFg+dKul2euXKFScShR
h6tknaycBcdNbA+6dQJo+VgrTTewvfrkpNyifPBwk9vIitRhFkJJJVGsR6T+AF/UJfY5dEYYFuu5
J288ggKjbjEUNQnIyNWOpZiuhpClTTay3laNkw==

`protect key_keyowner="ATRENTA", key_keyname="ATR-SG-2015-RSA-3", key_method="rsa"
`protect encoding = (enctype="BASE64", line_length=76, bytes=256)
`protect key_block
htKUMvAlzdN4BbAAeNmEM6Yr1UUCORwvd6+1cV737AnX/e5QyMGFY1ZuaVzrrzfIKK+VWd/bFDYR
WeL3jKvGUsyl0cMQ9jcxLrsCI3RnUD8yDbbqyDu9KMj34D7UA/k879CbEg7mJQsE/OUuwmk5Rusa
S2E+UVp+HrYNnNymuLmmn6wOTCKRZjZEMW81xyRvJrDTTqf12SjMprM/ubdETBwwiEzoIwLeibWv
EE77NEiYVwYpzXElBkB+JN+riXCrervjpMbAzHbeomW24pwXmffMMvkj1nRzaEI2QRT19Hpc4iqq
tT7PSLFxC6iyyFn2bd5a57kSCEK5ZaaxszxEVg==

`protect key_keyowner="Mentor Graphics Corporation", key_keyname="MGC-VELOCE-RSA", key_method="rsa"
`protect encoding = (enctype="BASE64", line_length=76, bytes=128)
`protect key_block
ST+OORnrF+3QguD7AuqTgC907V9FPxT3xpP2TfPbwAQB2+m85/czQ7xrlMYLNRNl2qldRPC2JAtf
yRLJmvKEgyRtR6tv/9gg66CdnvMVGbBmprZnmsgKpHGXcIGIVm6FR+ifL/5pZcFZyTQCKYlbE6bz
YNrIQ8EskAk5YXNHRZU=

`protect key_keyowner="Mentor Graphics Corporation", key_keyname="MGC-VERIF-SIM-RSA-2", key_method="rsa"
`protect encoding = (enctype="BASE64", line_length=76, bytes=256)
`protect key_block
Zz8HkbKk2BMn9pYqHdEWEMFHnKjJed8tZnBzajqsks1G6q0CzbV0FSYoWS1nKj84tIU1JkBaGDIt
9sdF4TFidxOJyhtrmpNfTChKxpMr41K8vo0yCOwdi29v/VShuI/rkIBCSgrdlmTBWBEgiBS9aabp
Jqqjo1ol263k6jlcp9rOjaoU+lcQMEXCkHoZu/V2+VWtTqhoSiWKgDQ0jJptGQig3wemEM16ctGQ
xX4urrzlEYCVTlr9g3mn6x8NgAjEFjJqmg1uE21AWGXfsNowkj2dYZLCXuVTF108ULXlOgx8TBHk
tPYc56T7eylPXV3Y05Z7agtvOLTYldGNSnm7qQ==

`protect key_keyowner="Real Intent", key_keyname="RI-RSA-KEY-1", key_method="rsa"
`protect encoding = (enctype="BASE64", line_length=76, bytes=256)
`protect key_block
VHzNHo3jyVixjpbjlcbNuO7IrIjCuYoXTAjRb06/SIYnbUS1pXATLQwryf5S2ETq0CYvThlIAGS0
xbNOLpEIhHMaY4VNrUdhUPBHXcXHWUCHudYKaUCB/Pk28QZKLuHYt3FqZh6wdzI6AFJdP/pykVJb
M/Pyyc+uLtqsAqyWqtJ0puNrBSpFPSM5259v7Gum4dwYGluRNUyJPq0CnQOQDcjaKw42cmf2DAtX
CSJb79mvoLdsFiW5ePQbcfrrcT/FhIkNj4/DqMVl2EB85zQgcPJw5Up3lLGw0Qd2Cd1jeq3A4qcf
LraHhfdfhy6tS33yDqFUeXlzvLfkicvxivScIw==

`protect key_keyowner="Xilinx", key_keyname="xilinxt_2020_08", key_method="rsa"
`protect encoding = (enctype="BASE64", line_length=76, bytes=256)
`protect key_block
Ir7vg+6icGbLB3CLLO2WEVH7p5OyaYzRs27g9ktjlLGEA8UZWJVD/LEebYJEdrotzhB8SWmHZMDV
/tU66bmEBeBvDhzPDFffP8JEne90WI2d4WsOz8gc/qUmQrWkWWpKaGeRzRKobk6HEaC+nXg3PqfM
0b03fbE0S205+4xE/rEnuHBIRBfZd3xmeVaB0HKBt0SGPD5SSQQZpPD38QOtCELjuuuA4RtmpS90
kaKEHc7Je6wpd85YQOJtbSfSfwms8QmBrV2vuYX5vgvFoWdrKhFu6ei5xOtYRK3gX3JKdEXLebbV
49uISo0iQ96Wfdc+51UDQD4Z2sSmPF/BKuQ5nQ==

`protect key_keyowner="Metrics Technologies Inc.", key_keyname="DSim", key_method="rsa"
`protect encoding = (enctype="BASE64", line_length=76, bytes=256)
`protect key_block
LpdRmMYH4gdKs52wqPlK6TsP8t36Rz9etYG+uFXIxoYPOw77GvCpHTnPEq4wgKvtHfjSBYM58T8o
VFR+rx+dgG80Vv61h2/ALXu7WMVNRnj432YN7jUfiNGlmdGjYf7j5bb6jDSZd9SGg9hOG322ua8w
FL0iNhZ1+8bqOC5DHZhVoYhtH7wentMTqEBB4I+Xy3zK2H07hbY20A+hZ5iviyCzHMtmQ5LCJzAb
8LeBnGRdOv8ntIJz3n1voQKFpamiYGRWqDwIHC+A3vf0VlEiw8M53hPC9SjoIQqQxSnkzTditbkH
fDStRcfPfMIOJ9yoREe7QoWlh0XCwpflnMvnNg==

`protect key_keyowner="Mentor Graphics Corporation", key_keyname="MGC-PREC-RSA", key_method="rsa"
`protect encoding = (enctype="BASE64", line_length=76, bytes=256)
`protect key_block
k3NZzEED9DLtKpAjlpvqJGN9tEXB91YGg1fP+EAgkW6bkFbK7SPQtPRFW5uuI2UGOGHAN/GtRnGN
2jtNXP4JsQlP8pHH4gHdL1zTnLLk4frfxADjhZW0fKmCQDdCmsC9KAFJU4FoyNMDOsryxf2bVoBz
flowOwjSVmrL5/SqyCLtfwmTN9x5+cX8EOlLKdPvz2dnGU9pGcSBLTSHXS8c9ZuLxpvwt4oIDquz
2oMp8NFWYGaZYLr/41qldkaG0Ro7PugkXgVJVR50jF/ycu/Ke5YwwHLRMFDwFcwTjNllrsbnn45X
6HKaEheO4420urgC/02DPZTE5dKaszLXmMz8oA==

`protect key_keyowner="Synplicity", key_keyname="SYNP15_1", key_method="rsa"
`protect encoding = (enctype="BASE64", line_length=76, bytes=256)
`protect key_block
cMBt64binfwY2bngOcoxbD9KdF4Wyptirb3S3gVg9SG0HKHezGg0MP2t++YoZ10ryd2h4FwalBP7
iXm/5CDOzMFLu0mcVtxEXR8jJql/lV3dG2VQup3iVAFsyFnG7yn6m3iLyqINstr+5PzLisA3fvMY
vmuS/6DWHHWFCQxvkBhKSzPoC9SOSKdQfrmYELK7L60ZEOlnfbHWX9eOXgDU3nY48h3jGTMH6awE
tZY8NgeOCQelAT1dE6li5szSgqHMmc2AJNdsAysZBQXCbg5PaLKgLDbWpggB++b/XWmO/QJcJG6c
y6QzefTuCNL2L9XVV9Vmhc3utRFYczNPbfATPA==

`protect data_method = "AES128-CBC"
`protect encoding = (enctype = "BASE64", line_length = 76, bytes = 17920)
`protect data_block
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
9Igks54g+wV9fLSAPl7wtXMplDEDRA==
`protect end_protected
`protect begin_protected
`protect version = 1
`protect encrypt_agent = "XILINX"
`protect encrypt_agent_info = "Xilinx Encryption Tool 2020.2"
`protect key_keyowner="Cadence Design Systems.", key_keyname="cds_rsa_key", key_method="rsa"
`protect encoding = (enctype="BASE64", line_length=76, bytes=64)
`protect key_block
WpplON9gajPqZwUKldyuoeqmBpIPSBxYcr5JWxrDlqNhqbxliKwmPwmbmeArplvGzrWaKVJ8yMLk
xTgTAsmnRg==

`protect key_keyowner="Synopsys", key_keyname="SNPS-VCS-RSA-2", key_method="rsa"
`protect encoding = (enctype="BASE64", line_length=76, bytes=128)
`protect key_block
PywlUwtIgAXcje485P53GElPqY0h5tEj5ZDYGG4C1L/pCl1vhbCpI4Lfv1uBUhTCUgt0vUUApdRs
K2IImoVdVbz1EI11gNNCxuGNEsj4QbnWfiiRUf8TsfVO4gWgHDJkD4RJc+jcEVx/ZrSadMs2mHy7
KNZCnUFKCidfdRy/hkw=

`protect key_keyowner="Aldec", key_keyname="ALDEC15_001", key_method="rsa"
`protect encoding = (enctype="BASE64", line_length=76, bytes=256)
`protect key_block
unxmOFx/kGsfl24PCNNEZkygDDk8LvPrdhRZmBKwU8hEl0IYKnNbmVzy0GX33C+cHqleOLdJYv/h
wKQu75v68Cl8qlEV1Vqfa7UnK7q4w6bLjBa9BHtnG7S/H0Ywr54xnAXnSKvxTDfYX2sDgkcwSXoh
X0q3YhQRNlz6nKs2p675XjlEojeW92VNoWv8pHj8MG/qmJ8VohHbQpf0YxozMcZpH0CF/Ozm/fua
Vyb99q8DdEkMUxP21j9+F/I46Pbkcvq9zC2FY4Mv+gYZfH461p3qA1P0UNBQRmRRkOCCOAxz3PHk
qsrTTWDzAK0GxdzwQ7cbJFKBbdBVaV6+4memyA==

`protect key_keyowner="ATRENTA", key_keyname="ATR-SG-2015-RSA-3", key_method="rsa"
`protect encoding = (enctype="BASE64", line_length=76, bytes=256)
`protect key_block
pA50PpjJaJ8uV4EV7d4QCm5ucA0irsAJKsW/2yhM7uxfdfY6+ycy5Dlu6AXQj787AwSOkZjihqnA
0ZuEvQsnWN+aN5ZJgO/zI+HLHFGLXVZBK4YXwqHRk9mh8mtXkERd+D/Ig8IyNAjqeNFZtCo2lzge
AowqsmCoC67eYhNG5p9fzPjDy5k+MEVGOvXR621zFn4wRLcANXbLLaqTgDI902JfKeuW3HE+NVjz
0kcqt1g2MHeO7vwLhiZFHoP5uU7phxW1PW5Y7GQhQXmnbxXYl2WKNQoAt9enH/W7IaH1Se4RY/MA
HR2SD6NxDpfgAqD/XrFGW0hzhzJlI6XWA2wiLw==

`protect key_keyowner="Mentor Graphics Corporation", key_keyname="MGC-VELOCE-RSA", key_method="rsa"
`protect encoding = (enctype="BASE64", line_length=76, bytes=128)
`protect key_block
Z2C5b5Vf7eNgxsVgM+blog4oljuJGPE5amBDDw4IFWKEcJNxmK8iNsR1/nSU618rRzWshK/Fg8uY
H1Fs2nnnxOsbeSPfDz60zapynorXwzsi0dI/KtefB5PI8A9PzP9LZmPF5GoKgCyeO5RXGRNhstIX
p1ezoG0hvuiDRGjlMKc=

`protect key_keyowner="Mentor Graphics Corporation", key_keyname="MGC-VERIF-SIM-RSA-2", key_method="rsa"
`protect encoding = (enctype="BASE64", line_length=76, bytes=256)
`protect key_block
et3u9Nh2LCj8dZdn07LM2qUls9+keyt7JsISbFOsxR6cpH5B16zv97Rzwn74yMYiUBGAvUZ1T1v0
O4vr5rGCW0AQjy4M5nemZ9M6vuyPMPAob/tFs+R7Jb9fpt8qHPEH64ni3rOSEVPe07L1FARbFVCK
LUHHDuIaqTmTbQ20cYPgWi7rOJGYZaRI6TwujcBF5oJDmg+gry6t509xfzd/HPgX+tLX6NJuYBCP
ePAG3UjlqodSXw8U64081MNLzzmsSrNe2EnZfEXP2ODfphEFJ/9pYKdR8lyWMJQ6+Pu3vdvO+IIy
c0Cghu/ZzVtvJ7/zrgoR8hCFeuBzbeRvdhR5Fg==

`protect key_keyowner="Real Intent", key_keyname="RI-RSA-KEY-1", key_method="rsa"
`protect encoding = (enctype="BASE64", line_length=76, bytes=256)
`protect key_block
m2Nc/hOcqeBJFQqyL9SEkYAeLvPo2q4UIb79AxfyebsFVgipkPXe9Fr2Ly0oEBcpASNJVxE/qNX1
ncav7fcSQJ3AUai6lNvLIkrtdkVBATFfCbWr3T9gTPaXD1ZY1pnli57FrU8DixIaFRoeIg2lfWgX
Ejddks6fcCByoDETUKwOz1fhlUulegwij55Z9od8zC/RPnW2JzX7L7mQWAla4j7M4VzHtS/8AzAP
IcrhT+J0DDWfBDrYcYDo/5IL9X+cSnPrj3CzqrbyEBZ9J0tyVT8g9z9bEph9htiA9EuYQVcpbIB1
qmVC7LtsXr7t9qeijbb4dFcovnX3H5CRc3Xybg==

`protect key_keyowner="Xilinx", key_keyname="xilinxt_2020_08", key_method="rsa"
`protect encoding = (enctype="BASE64", line_length=76, bytes=256)
`protect key_block
UPKDuDrUpCqZq5As9ryjcITL7qO0/Aj65ai6MGkRJ5fsdrAIoRtKd/gZdMexAxpHxy5h8KvNWciR
45oibPZHqHo46BRzAtonK7cDtSPx2RaIzOvjoexdDjwbvwPqiCJhCul2J8EsDU1WPbSUWx7vpKn+
MYAq9BJrKBfkewHr8CqWmQugmrAbTxft49DV5mIiIEOhVCOTMV21e+pl1SODhXcx/d88X1XTvMY+
OkEL+ZPfyhoGAg9Tj5WjHVoAT0XcCjHObI3kOJqt3hPr2RYm1+yghuhT5ntdvMHa6iEBG/En+ah4
sN9yhdXkV5VsiSpxp/EsAX5tQkOiDZCtXXHNeQ==

`protect key_keyowner="Metrics Technologies Inc.", key_keyname="DSim", key_method="rsa"
`protect encoding = (enctype="BASE64", line_length=76, bytes=256)
`protect key_block
rBmtHpx5e1XZPx6PBIEZ/58/PYTolg3kUSJ5yidwAgHM+vcWKSyMd/LXtLj20j7EpJVceIapdGYF
4nkL9OaJnw2p3gO+zvHk44FY2WlPcGjJ9qy4Z8049p1vFldJbTCwn8j2kMzXfA1XD0ll2p+WVUVI
EDJhvfyMnZOPwoecUCmOKjFhw7Oe93CtOZTTQI+gL+gADbsYMQ4cpMYr3spVh2jDfyhZRzb4Bm5h
ZlvJFfItmnW4/YJNUbQXoE22pLPLOaoAtOONuU5fFYk7jrQlcGNSRbnIf7aS7oW0kJmbes5lzfoD
QmLyp2jy+Pig+uTYrKUU4x0GRLNhdkoO25o5ew==

`protect data_method = "AES128-CBC"
`protect encoding = (enctype = "BASE64", line_length = 76, bytes = 6032)
`protect data_block
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
`protect end_protected
library IEEE;
use IEEE.STD_LOGIC_1164.ALL;
library UNISIM;
use UNISIM.VCOMPONENTS.ALL;
entity top_c_counter_binary_i_0 is
  port (
    CLK : in STD_LOGIC;
    Q : out STD_LOGIC_VECTOR ( 13 downto 0 )
  );
  attribute NotValidForBitStream : boolean;
  attribute NotValidForBitStream of top_c_counter_binary_i_0 : entity is true;
  attribute CHECK_LICENSE_TYPE : string;
  attribute CHECK_LICENSE_TYPE of top_c_counter_binary_i_0 : entity is "top_c_counter_binary_i_0,c_counter_binary_v12_0_14,{}";
  attribute downgradeipidentifiedwarnings : string;
  attribute downgradeipidentifiedwarnings of top_c_counter_binary_i_0 : entity is "yes";
  attribute x_core_info : string;
  attribute x_core_info of top_c_counter_binary_i_0 : entity is "c_counter_binary_v12_0_14,Vivado 2020.2";
end top_c_counter_binary_i_0;

architecture STRUCTURE of top_c_counter_binary_i_0 is
  signal NLW_U0_THRESH0_UNCONNECTED : STD_LOGIC;
  attribute C_AINIT_VAL : string;
  attribute C_AINIT_VAL of U0 : label is "0";
  attribute C_CE_OVERRIDES_SYNC : integer;
  attribute C_CE_OVERRIDES_SYNC of U0 : label is 0;
  attribute C_FB_LATENCY : integer;
  attribute C_FB_LATENCY of U0 : label is 0;
  attribute C_HAS_CE : integer;
  attribute C_HAS_CE of U0 : label is 0;
  attribute C_HAS_SCLR : integer;
  attribute C_HAS_SCLR of U0 : label is 0;
  attribute C_HAS_SINIT : integer;
  attribute C_HAS_SINIT of U0 : label is 0;
  attribute C_HAS_SSET : integer;
  attribute C_HAS_SSET of U0 : label is 0;
  attribute C_IMPLEMENTATION : integer;
  attribute C_IMPLEMENTATION of U0 : label is 0;
  attribute C_SCLR_OVERRIDES_SSET : integer;
  attribute C_SCLR_OVERRIDES_SSET of U0 : label is 1;
  attribute C_SINIT_VAL : string;
  attribute C_SINIT_VAL of U0 : label is "0";
  attribute C_VERBOSITY : integer;
  attribute C_VERBOSITY of U0 : label is 0;
  attribute C_WIDTH : integer;
  attribute C_WIDTH of U0 : label is 14;
  attribute C_XDEVICEFAMILY : string;
  attribute C_XDEVICEFAMILY of U0 : label is "spartan7";
  attribute c_count_by : string;
  attribute c_count_by of U0 : label is "10001";
  attribute c_count_mode : integer;
  attribute c_count_mode of U0 : label is 0;
  attribute c_count_to : string;
  attribute c_count_to of U0 : label is "1";
  attribute c_has_load : integer;
  attribute c_has_load of U0 : label is 0;
  attribute c_has_thresh0 : integer;
  attribute c_has_thresh0 of U0 : label is 0;
  attribute c_latency : integer;
  attribute c_latency of U0 : label is 1;
  attribute c_load_low : integer;
  attribute c_load_low of U0 : label is 0;
  attribute c_restrict_count : integer;
  attribute c_restrict_count of U0 : label is 0;
  attribute c_thresh0_value : string;
  attribute c_thresh0_value of U0 : label is "1";
  attribute downgradeipidentifiedwarnings of U0 : label is "yes";
  attribute is_du_within_envelope : string;
  attribute is_du_within_envelope of U0 : label is "true";
  attribute x_interface_info : string;
  attribute x_interface_info of CLK : signal is "xilinx.com:signal:clock:1.0 clk_intf CLK";
  attribute x_interface_parameter : string;
  attribute x_interface_parameter of CLK : signal is "XIL_INTERFACENAME clk_intf, ASSOCIATED_BUSIF q_intf:thresh0_intf:l_intf:load_intf:up_intf:sinit_intf:sset_intf, ASSOCIATED_RESET SCLR, ASSOCIATED_CLKEN CE, FREQ_HZ 125000000, FREQ_TOLERANCE_HZ 0, PHASE 0.000, CLK_DOMAIN top_clk, INSERT_VIP 0";
  attribute x_interface_info of Q : signal is "xilinx.com:signal:data:1.0 q_intf DATA";
  attribute x_interface_parameter of Q : signal is "XIL_INTERFACENAME q_intf, LAYERED_METADATA xilinx.com:interface:datatypes:1.0 {DATA {datatype {name {attribs {resolve_type immediate dependency {} format string minimum {} maximum {}} value data} bitwidth {attribs {resolve_type generated dependency bitwidth format long minimum {} maximum {}} value 14} bitoffset {attribs {resolve_type immediate dependency {} format long minimum {} maximum {}} value 0} integer {signed {attribs {resolve_type immediate dependency {} format bool minimum {} maximum {}} value false}}}} DATA_WIDTH 14}";
begin
U0: entity work.top_c_counter_binary_i_0_c_counter_binary_v12_0_14
     port map (
      CE => '1',
      CLK => CLK,
      L(13 downto 0) => B"00000000000000",
      LOAD => '0',
      Q(13 downto 0) => Q(13 downto 0),
      SCLR => '0',
      SINIT => '0',
      SSET => '0',
      THRESH0 => NLW_U0_THRESH0_UNCONNECTED,
      UP => '1'
    );
end STRUCTURE;
