simonyiszk/open-hf-sdr/vivado/ha5kfu_ws2/ha5kfu_ws2.srcs/sources_1/bd/top/ip/top_dds_compiler_0_0/top_dds_compiler_0_0_sim_netlist.v

// Copyright 1986-2020 Xilinx, Inc. All Rights Reserved.
// --------------------------------------------------------------------------------
// Tool Version: Vivado v.2020.2 (win64) Build 3064766 Wed Nov 18 09:12:45 MST 2020
// Date        : Fri Feb 12 23:07:28 2021
// Host        : RemoteApp running 64-bit major release  (build 9200)
// Command     : write_verilog -force -mode funcsim -rename_top top_dds_compiler_0_0 -prefix
//               top_dds_compiler_0_0_ top_dds_compiler_0_0_sim_netlist.v
// Design      : top_dds_compiler_0_0
// Purpose     : This verilog netlist is a functional simulation representation of the design and should not be modified
//               or synthesized. This netlist cannot be used for SDF annotated simulation.
// Device      : xc7s6ftgb196-1
// --------------------------------------------------------------------------------
`timescale 1 ps / 1 ps

(* CHECK_LICENSE_TYPE = "top_dds_compiler_0_0,dds_compiler_v6_0_20,{}" *) (* downgradeipidentifiedwarnings = "yes" *) (* x_core_info = "dds_compiler_v6_0_20,Vivado 2020.2" *) 
(* NotValidForBitStream *)
module top_dds_compiler_0_0
   (aclk,
    s_axis_config_tvalid,
    s_axis_config_tdata,
    m_axis_data_tvalid,
    m_axis_data_tdata,
    m_axis_phase_tvalid,
    m_axis_phase_tdata);
  (* x_interface_info = "xilinx.com:signal:clock:1.0 aclk_intf CLK" *) (* x_interface_parameter = "XIL_INTERFACENAME aclk_intf, ASSOCIATED_BUSIF M_AXIS_PHASE:S_AXIS_CONFIG:M_AXIS_DATA:S_AXIS_PHASE, ASSOCIATED_RESET aresetn, ASSOCIATED_CLKEN aclken, FREQ_HZ 125000000, FREQ_TOLERANCE_HZ 0, PHASE 0.000, CLK_DOMAIN top_clk, INSERT_VIP 0" *) input aclk;
  (* x_interface_info = "xilinx.com:interface:axis:1.0 S_AXIS_CONFIG TVALID" *) (* x_interface_parameter = "XIL_INTERFACENAME S_AXIS_CONFIG, TDATA_NUM_BYTES 8, TDEST_WIDTH 0, TID_WIDTH 0, TUSER_WIDTH 0, HAS_TREADY 0, HAS_TSTRB 0, HAS_TKEEP 0, HAS_TLAST 0, FREQ_HZ 125000000, PHASE 0.000, CLK_DOMAIN top_clk, LAYERED_METADATA undef, INSERT_VIP 0" *) input s_axis_config_tvalid;
  (* x_interface_info = "xilinx.com:interface:axis:1.0 S_AXIS_CONFIG TDATA" *) input [63:0]s_axis_config_tdata;
  (* x_interface_info = "xilinx.com:interface:axis:1.0 M_AXIS_DATA TVALID" *) (* x_interface_parameter = "XIL_INTERFACENAME M_AXIS_DATA, TDATA_NUM_BYTES 2, TDEST_WIDTH 0, TID_WIDTH 0, TUSER_WIDTH 0, HAS_TREADY 0, HAS_TSTRB 0, HAS_TKEEP 0, HAS_TLAST 0, FREQ_HZ 125000000, PHASE 0.000, CLK_DOMAIN top_c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
  (* x_interface_info = "xilinx.com:interface:axis:1.0 M_AXIS_DATA TDATA" *) output [15:0]m_axis_data_tdata;
  (* x_interface_info = "xilinx.com:interface:axis:1.0 M_AXIS_PHASE TVALID" *) (* x_interface_parameter = "XIL_INTERFACENAME M_AXIS_PHASE, TDATA_NUM_BYTES 4, TDEST_WIDTH 0, TID_WIDTH 0, TUSER_WIDTH 0, HAS_TREADY 0, HAS_TSTRB 0, HAS_TKEEP 0, HAS_TLAST 0, FREQ_HZ 125000000, PHASE 0.000, CLK_DOMAIN top_clk, LAYERED_METADATA xilinx.com:interface:datatypes:1.0 {TDATA {datatype {name {attribs {resolve_type immediate dependency {} format string minimum {} maximum {}} value {}} bitwidth {attribs {resolve_type automatic dependency {} format long minimum {} maximum {}} value 27} bitoffset {attribs {resolve_type immediate dependency {} format long minimum {} maximum {}} value 0} array_type {name {attribs {resolve_type immediate dependency {} format string minimum {} maximum {}} value chan} size {attribs {resolve_type generated dependency chan_size format long minimum {} maximum {}} value 1} stride {attribs {resolve_type generated dependency chan_stride format long minimum {} maximum {}} value 32} datatype {name {attribs {resolve_type immediate dependency {} format string minimum {} maximum {}} value {}} bitwidth {attribs {resolve_type automatic dependency {} format long minimum {} maximum {}} value 27} bitoffset {attribs {resolve_type immediate dependency {} format long minimum {} maximum {}} value 0} struct {field_phase_out {name {attribs {resolve_type immediate dependency {} format string minimum {} maximum {}} value phase_out} enabled {attribs {resolve_type immediate dependency {} format bool minimum {} maximum {}} value true} datatype {name {attribs {resolve_type immediate dependency {} format string minimum {} maximum {}} value {}} bitwidth {attribs {resolve_type generated dependency phase_width format long minimum {} maximum {}} value 27} bitoffset {attribs {resolve_type immediate dependency {} format long minimum {} maximum {}} value 0} real {fixed {fractwidth {attribs {resolve_type generated dependency phase_fractwidth format long minimum {} maximum {}} value 27} signed {attribs {resolve_type immediate dependency {} format bool minimum {} maximum {}} value false}}}}}}}}}} TDATA_WIDTH 32 TUSER {datatype {name {attribs {resolve_type immediate dependency {} format string minimum {} maximum {}} value {}} bitwidth {attribs {resolve_type automatic dependency {} format long minimum {} maximum {}} value 0} bitoffset {attribs {resolve_type immediate dependency {} format long minimum {} maximum {}} value 0} struct {field_chanid {name {attribs {resolve_type immediate dependency {} format string minimum {} maximum {}} value chanid} enabled {attribs {resolve_type generated dependency chanid_enabled format bool minimum {} maximum {}} value false} datatype {name {attribs {resolve_type immediate dependency {} format string minimum {} maximum {}} value {}} bitwidth {attribs {resolve_type generated dependency chanid_width format long minimum {} maximum {}} value 0} bitoffset {attribs {resolve_type immediate dependency {} format long minimum {} maximum {}} value 0} integer {signed {attribs {resolve_type immediate dependency {} format bool minimum {} maximum {}} value false}}}} field_user {name {attribs {resolve_type immediate dependency {} format string minimum {} maximum {}} value user} enabled {attribs {resolve_type generated dependency user_enabled format bool minimum {} maximum {}} value false} datatype {name {attribs {resolve_type immediate dependency {} format string minimum {} maximum {}} value {}} bitwidth {attribs {resolve_type generated dependency user_width format long minimum {} maximum {}} value 0} bitoffset {attribs {resolve_type generated dependency user_offset format long minimum {} maximum {}} value 0}}}}}} TUSER_WIDTH 0}, INSERT_VIP 0" *) output m_axis_phase_tvalid;
  (* x_interface_info = "xilinx.com:interface:axis:1.0 M_AXIS_PHASE TDATA" *) output [31:0]m_axis_phase_tdata;

  wire aclk;
  wire [15:0]m_axis_data_tdata;
  wire m_axis_data_tvalid;
  wire [31:0]m_axis_phase_tdata;
  wire m_axis_phase_tvalid;
  wire [63:0]s_axis_config_tdata;
  wire s_axis_config_tvalid;
  wire NLW_U0_debug_axi_resync_in_UNCONNECTED;
  wire NLW_U0_debug_core_nd_UNCONNECTED;
  wire NLW_U0_debug_phase_nd_UNCONNECTED;
  wire NLW_U0_event_phase_in_invalid_UNCONNECTED;
  wire NLW_U0_event_pinc_invalid_UNCONNECTED;
  wire NLW_U0_event_poff_invalid_UNCONNECTED;
  wire NLW_U0_event_s_config_tlast_missing_UNCONNECTED;
  wire NLW_U0_event_s_config_tlast_unexpected_UNCONNECTED;
  wire NLW_U0_event_s_phase_chanid_incorrect_UNCONNECTED;
  wire NLW_U0_event_s_phase_tlast_missing_UNCONNECTED;
  wire NLW_U0_event_s_phase_tlast_unexpected_UNCONNECTED;
  wire NLW_U0_m_axis_data_tlast_UNCONNECTED;
  wire NLW_U0_m_axis_phase_tlast_UNCONNECTED;
  wire NLW_U0_s_axis_config_tready_UNCONNECTED;
  wire NLW_U0_s_axis_phase_tready_UNCONNECTED;
  wire [0:0]NLW_U0_debug_axi_chan_in_UNCONNECTED;
  wire [26:0]NLW_U0_debug_axi_pinc_in_UNCONNECTED;
  wire [26:0]NLW_U0_debug_axi_poff_in_UNCONNECTED;
  wire [26:0]NLW_U0_debug_phase_UNCONNECTED;
  wire [0:0]NLW_U0_m_axis_data_tuser_UNCONNECTED;
  wire [0:0]NLW_U0_m_axis_phase_tuser_UNCONNECTED;

  (* C_ACCUMULATOR_WIDTH = "27" *) 
  (* C_AMPLITUDE = "0" *) 
  (* C_CHANNELS = "1" *) 
  (* C_CHAN_WIDTH = "1" *) 
  (* C_DEBUG_INTERFACE = "0" *) 
  (* C_HAS_ACLKEN = "0" *) 
  (* C_HAS_ARESETN = "0" *) 
  (* C_HAS_M_DATA = "1" *) 
  (* C_HAS_M_PHASE = "1" *) 
  (* C_HAS_PHASEGEN = "1" *) 
  (* C_HAS_PHASE_OUT = "1" *) 
  (* C_HAS_SINCOS = "1" *) 
  (* C_HAS_S_CONFIG = "1" *) 
  (* C_HAS_S_PHASE = "0" *) 
  (* C_HAS_TLAST = "0" *) 
  (* C_HAS_TREADY = "0" *) 
  (* C_LATENCY = "4" *) 
  (* C_MEM_TYPE = "1" *) 
  (* C_MODE_OF_OPERATION = "0" *) 
  (* C_MODULUS = "9" *) 
  (* C_M_DATA_HAS_TUSER = "0" *) 
  (* C_M_DATA_TDATA_WIDTH = "16" *) 
  (* C_M_DATA_TUSER_WIDTH = "1" *) 
  (* C_M_PHASE_HAS_TUSER = "0" *) 
  (* C_M_PHASE_TDATA_WIDTH = "32" *) 
  (* C_M_PHASE_TUSER_WIDTH = "1" *) 
  (* C_NEGATIVE_COSINE = "0" *) 
  (* C_NEGATIVE_SINE = "0" *) 
  (* C_NOISE_SHAPING = "0" *) 
  (* C_OPTIMISE_GOAL = "0" *) 
  (* C_OUTPUTS_REQUIRED = "2" *) 
  (* C_OUTPUT_FORM = "0" *) 
  (* C_OUTPUT_WIDTH = "8" *) 
  (* C_PHASE_ANGLE_WIDTH = "8" *) 
  (* C_PHASE_INCREMENT = "1" *) 
  (* C_PHASE_INCREMENT_VALUE = "0,0,0,0,0,0,0,0,0,0,0,0,0,0,0,0" *) 
  (* C_PHASE_OFFSET = "1" *) 
  (* C_PHASE_OFFSET_VALUE = "0,0,0,0,0,0,0,0,0,0,0,0,0,0,0,0" *) 
  (* C_POR_MODE = "0" *) 
  (* C_RESYNC = "0" *) 
  (* C_S_CONFIG_SYNC_MODE = "0" *) 
  (* C_S_CONFIG_TDATA_WIDTH = "64" *) 
  (* C_S_PHASE_HAS_TUSER = "0" *) 
  (* C_S_PHASE_TDATA_WIDTH = "1" *) 
  (* C_S_PHASE_TUSER_WIDTH = "1" *) 
  (* C_USE_DSP48 = "0" *) 
  (* C_XDEVICEFAMILY = "spartan7" *) 
  (* downgradeipidentifiedwarnings = "yes" *) 
  (* is_du_within_envelope = "true" *) 
  top_dds_compiler_0_0_dds_compiler_v6_0_20 U0
       (.aclk(aclk),
        .aclken(1'b1),
        .aresetn(1'b1),
        .debug_axi_chan_in(NLW_U0_debug_axi_chan_in_UNCONNECTED[0]),
        .debug_axi_pinc_in(NLW_U0_debug_axi_pinc_in_UNCONNECTED[26:0]),
        .debug_axi_poff_in(NLW_U0_debug_axi_poff_in_UNCONNECTED[26:0]),
        .debug_axi_resync_in(NLW_U0_debug_axi_resync_in_UNCONNECTED),
        .debug_core_nd(NLW_U0_debug_core_nd_UNCONNECTED),
        .debug_phase(NLW_U0_debug_phase_UNCONNECTED[26:0]),
        .debug_phase_nd(NLW_U0_debug_phase_nd_UNCONNECTED),
        .event_phase_in_invalid(NLW_U0_event_phase_in_invalid_UNCONNECTED),
        .event_pinc_invalid(NLW_U0_event_pinc_invalid_UNCONNECTED),
        .event_poff_invalid(NLW_U0_event_poff_invalid_UNCONNECTED),
        .event_s_config_tlast_missing(NLW_U0_event_s_config_tlast_missing_UNCONNECTED),
        .event_s_config_tlast_unexpected(NLW_U0_event_s_config_tlast_unexpected_UNCONNECTED),
        .event_s_phase_chanid_incorrect(NLW_U0_event_s_phase_chanid_incorrect_UNCONNECTED),
        .event_s_phase_tlast_missing(NLW_U0_event_s_phase_tlast_missing_UNCONNECTED),
        .event_s_phase_tlast_unexpected(NLW_U0_event_s_phase_tlast_unexpected_UNCONNECTED),
        .m_axis_data_tdata(m_axis_data_tdata),
        .m_axis_data_tlast(NLW_U0_m_axis_data_tlast_UNCONNECTED),
        .m_axis_data_tready(1'b0),
        .m_axis_data_tuser(NLW_U0_m_axis_data_tuser_UNCONNECTED[0]),
        .m_axis_data_tvalid(m_axis_data_tvalid),
        .m_axis_phase_tdata(m_axis_phase_tdata),
        .m_axis_phase_tlast(NLW_U0_m_axis_phase_tlast_UNCONNECTED),
        .m_axis_phase_tready(1'b0),
        .m_axis_phase_tuser(NLW_U0_m_axis_phase_tuser_UNCONNECTED[0]),
        .m_axis_phase_tvalid(m_axis_phase_tvalid),
        .s_axis_config_tdata({1'b0,1'b0,1'b0,1'b0,1'b0,s_axis_config_tdata[58:32],1'b0,1'b0,1'b0,1'b0,1'b0,s_axis_config_tdata[26:0]}),
        .s_axis_config_tlast(1'b0),
        .s_axis_config_tready(NLW_U0_s_axis_config_tready_UNCONNECTED),
        .s_axis_config_tvalid(s_axis_config_tvalid),
        .s_axis_phase_tdata(1'b0),
        .s_axis_phase_tlast(1'b0),
        .s_axis_phase_tready(NLW_U0_s_axis_phase_tready_UNCONNECTED),
        .s_axis_phase_tuser(1'b0),
        .s_axis_phase_tvalid(1'b0));
endmodule
`pragma protect begin_protected
`pragma protect version = 1
`pragma protect encrypt_agent = "XILINX"
`pragma protect encrypt_agent_info = "Xilinx Encryption Tool 2020.2"
`pragma protect key_keyowner="Cadence Design Systems.", key_keyname="cds_rsa_key", key_method="rsa"
`pragma protect encoding = (enctype="BASE64", line_length=76, bytes=64)
`pragma protect key_block
ZhH7Or7GCAhAFpiSiK8r6sA7RwjJ9Tdii11EzwiypNpPn0r9A7rJiiZol84XxYNanpwTLFPRwdF3
O17/caqkTg==

`pragma protect key_keyowner="Synopsys", key_keyname="SNPS-VCS-RSA-2", key_method="rsa"
`pragma protect encoding = (enctype="BASE64", line_length=76, bytes=128)
`pragma protect key_block
ojNAWo89+4CzZxOHvA45GVT0ANL90cKmvVUXXwDB3fYmp9A9JzMVd1jVDc2C6zq40HRJI3LCtqYa
SANm7EdbxrlwmiFka/Vi1pmGwcvpHiXNHqEL40Ybr2rzaDJ/8s1TFl1xPgk91nvMuEUJ7Zn2ncWy
O4fQj9khXHZjQEY0hCk=

`pragma protect key_keyowner="Aldec", key_keyname="ALDEC15_001", key_method="rsa"
`pragma protect encoding = (enctype="BASE64", line_length=76, bytes=256)
`pragma protect key_block
ALgZm8VrZWZvRIch4Br8F+SMV+QwzLgh4lhQ7l513y3OWEbGpnpl2ftnp0u/2xp6nc3McskfP6nm
PJIcZIlaoKToyc9ZRjlnu3qXdjqRKZiEy2ry6na1WNvAIaoQUm6cedQIfaS44sUErPv5Hny28v01
jQKfzwV2u2/WdDSpq9G8hOJmD8cQ3zZchT3gKLO9morrDng3GunTKEfwYc3psoRS0ADCiN8q34xa
B0V0mmxTng2mAObVTR5v4uBWpsqq4e715mqrEjAgTT2TiRmhZA6iEH0d/cullajmHuhhllApBMPr
NQ7v5B4A3oTiYslgvPfU5+fjwE/t5C4ngf7cMQ==

`pragma protect key_keyowner="ATRENTA", key_keyname="ATR-SG-2015-RSA-3", key_method="rsa"
`pragma protect encoding = (enctype="BASE64", line_length=76, bytes=256)
`pragma protect key_block
NqL8mDDVaKZ5Rhf5kFotnTPpOfKK0XotF1IfCUjg/fLWMIgs9842rKKunnwWG4yl52a73CWOqlIU
wym62ZKwHQvNIhDYV4et8nOJ/ssF4L531FMXWk+Ax18Dho+Deap2g0iGf+xYvOf58mhjEUs+4Lpb
l6JQqgQz0Qvcux7Nb7vhRavZyxh1+omPDBi0rWxmBAAx6/3ruQBSwQYJCOtZByjb7cyYwaK2a5O+
gc37qC3xTorqIs13YdItFsS1XcyP9S+H98hyqMQtkTj9WbauO5PJXF9TgC7AZZdA6e7iPoo1P0MR
lxYNKo2yPtUYV/yEo48zAFaT6y9MWELY9FWX0w==

`pragma protect key_keyowner="Mentor Graphics Corporation", key_keyname="MGC-VELOCE-RSA", key_method="rsa"
`pragma protect encoding = (enctype="BASE64", line_length=76, bytes=128)
`pragma protect key_block
d4Ir9YmkpeWxfTLlPQYtgkUeaxN8B1i90JFB7P9JRLI2mXpcAqbM1Ddckph49f+F/oHMkaQ1Dzdy
Tej6kxJi/Wdiu5rZ5OmBuS1ZbOG2CJC6XfXj0ThvxQ1LW4KNfufD8drKKx2IixrN1qv0PX60j/6X
3tXvEQ4xFipk/uBl74M=

`pragma protect key_keyowner="Mentor Graphics Corporation", key_keyname="MGC-VERIF-SIM-RSA-2", key_method="rsa"
`pragma protect encoding = (enctype="BASE64", line_length=76, bytes=256)
`pragma protect key_block
AcG3M3dwdYa7Crux6whvnEB7jpQ3vYcVRjQE5IC/udJBxEWpsGpVQvccMKBkoDHqdapYFU/iis0y
URrcLRxuH1iKJfzTcPj3UrIKQD9hZrAokyeBmOtsQ+XAWjJkJU85Qm3Ik0ZRBpB/TLb4/lT75yA7
UVZ90xB7V73bMURI+0oh6pjmcYbZ1CLO3wNCtVzFBzmngbfwzsRdxSArLHEd3e5VZpxrrhdclpzu
0l0xLi8XYPn9IoQcyVJfd34Oj5C6xjuozB8+xokj5qXDryDzLxGuS1qWUi55uL8EBiv81cZoNk/O
K6JvjMhV3Byr7N02AfkTJtDyXNgRm5QsOdQIIQ==

`pragma protect key_keyowner="Real Intent", key_keyname="RI-RSA-KEY-1", key_method="rsa"
`pragma protect encoding = (enctype="BASE64", line_length=76, bytes=256)
`pragma protect key_block
s7hXRgGD7PplS4pBVEYIAD7ljzuh25HUgBtLBeE/2ImUhn/63TjM1VrWBdMEmMOCTVMAMtVjdkQW
NS+ZyPExJTiGBpj5ZS0pPGflQ6V7uW6IpfHQ6aa9mRriWcZ4TuEr3yMtE+luDo6Chw0hgizpV5By
lGPXBz9qv4Z/PSwxAtCxO/ksyRObQ9glxV/ECfAE/lIKYwJ+/WaCNIGStPhoMB6/bo6ZBAVbZ8wx
PuM5xkRe1qTNlQSqCRqnrSvSGG6JoxHfLwN4Y61rUk9XF6mr0zxKpwONVqkYd73dCWsbtsywPXhv
u4Gcx00Vud2slvSdQXyCJiSRTblaZrSdOApVCQ==

`pragma protect key_keyowner="Xilinx", key_keyname="xilinxt_2020_08", key_method="rsa"
`pragma protect encoding = (enctype="BASE64", line_length=76, bytes=256)
`pragma protect key_block
ZckK18NWTOr3bQxeTQ2Hmehew8edLI59NtFiD96pysefOkcdqoNSDc6Q21XYVaYLKX0lYNCW/c6n
fv5C4G0fE7A80b0SPkQE+sipaiBKWBNNb7GwGwwySLCePoDtZybeOvpqvvaxadDa0dqtQJbA4Zgj
LzcT0GMgIQgj84Z3Eu8ooI5jQk9jwAPKrZcdar/xrnoD2kI5ELzXQbNAj6Di5OEO91+HAv8WphCC
mruqWvwON3yyTxqzXEmugM0Ro7iCh5ErefC7ej8IJ8xoJ4++2UlBwwue5mPA5gNYhtQkFcQ7Np1e
Ycs+gyHI/UVizRd+96zJ57Sq5tf88tJ9NQqRfA==

`pragma protect key_keyowner="Metrics Technologies Inc.", key_keyname="DSim", key_method="rsa"
`pragma protect encoding = (enctype="BASE64", line_length=76, bytes=256)
`pragma protect key_block
Rws6+VMWmHV6kQwKOlrBwauV6Z4saZJvIT7vO0puMXJlcaRlIvoj5ogg/v58Ri3VQEE9fMChgryM
pyKqZnjLcwA7Y2k+uXNfhwaaHv00BPIfbb7kyG3qs00Ja2TNlJI4WJsoMo88a5AbTegYyaQ8vJaM
0GjbbTcOuG8re5lVCUM0FM1b/1k7+iQp6Klfmh9VtIYk5dhuAyQHMRFGmOSfdE27bffNgdfYS3kp
i0DtbgNnRIDsdIlu2/RO3GojLf+2oyIm6Zf4ORn5bjGq4hduIv0GFaYbpasBvNnpNjRbeA0hPZcR
ouMej74eTG4+j2Xu7Kl+tvKu2e2a0zAkb0Z6Cg==

`pragma protect data_method = "AES128-CBC"
`pragma protect encoding = (enctype = "BASE64", line_length = 76, bytes = 13456)
`pragma protect data_block
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
7QF/og==
`pragma protect end_protected
`pragma protect begin_protected
`pragma protect version = 1
`pragma protect encrypt_agent = "XILINX"
`pragma protect encrypt_agent_info = "Xilinx Encryption Tool 2020.2"
`pragma protect key_keyowner="Cadence Design Systems.", key_keyname="cds_rsa_key", key_method="rsa"
`pragma protect encoding = (enctype="BASE64", line_length=76, bytes=64)
`pragma protect key_block
ZhH7Or7GCAhAFpiSiK8r6sA7RwjJ9Tdii11EzwiypNpPn0r9A7rJiiZol84XxYNanpwTLFPRwdF3
O17/caqkTg==

`pragma protect key_keyowner="Synopsys", key_keyname="SNPS-VCS-RSA-2", key_method="rsa"
`pragma protect encoding = (enctype="BASE64", line_length=76, bytes=128)
`pragma protect key_block
ojNAWo89+4CzZxOHvA45GVT0ANL90cKmvVUXXwDB3fYmp9A9JzMVd1jVDc2C6zq40HRJI3LCtqYa
SANm7EdbxrlwmiFka/Vi1pmGwcvpHiXNHqEL40Ybr2rzaDJ/8s1TFl1xPgk91nvMuEUJ7Zn2ncWy
O4fQj9khXHZjQEY0hCk=

`pragma protect key_keyowner="Aldec", key_keyname="ALDEC15_001", key_method="rsa"
`pragma protect encoding = (enctype="BASE64", line_length=76, bytes=256)
`pragma protect key_block
ALgZm8VrZWZvRIch4Br8F+SMV+QwzLgh4lhQ7l513y3OWEbGpnpl2ftnp0u/2xp6nc3McskfP6nm
PJIcZIlaoKToyc9ZRjlnu3qXdjqRKZiEy2ry6na1WNvAIaoQUm6cedQIfaS44sUErPv5Hny28v01
jQKfzwV2u2/WdDSpq9G8hOJmD8cQ3zZchT3gKLO9morrDng3GunTKEfwYc3psoRS0ADCiN8q34xa
B0V0mmxTng2mAObVTR5v4uBWpsqq4e715mqrEjAgTT2TiRmhZA6iEH0d/cullajmHuhhllApBMPr
NQ7v5B4A3oTiYslgvPfU5+fjwE/t5C4ngf7cMQ==

`pragma protect key_keyowner="ATRENTA", key_keyname="ATR-SG-2015-RSA-3", key_method="rsa"
`pragma protect encoding = (enctype="BASE64", line_length=76, bytes=256)
`pragma protect key_block
NqL8mDDVaKZ5Rhf5kFotnTPpOfKK0XotF1IfCUjg/fLWMIgs9842rKKunnwWG4yl52a73CWOqlIU
wym62ZKwHQvNIhDYV4et8nOJ/ssF4L531FMXWk+Ax18Dho+Deap2g0iGf+xYvOf58mhjEUs+4Lpb
l6JQqgQz0Qvcux7Nb7vhRavZyxh1+omPDBi0rWxmBAAx6/3ruQBSwQYJCOtZByjb7cyYwaK2a5O+
gc37qC3xTorqIs13YdItFsS1XcyP9S+H98hyqMQtkTj9WbauO5PJXF9TgC7AZZdA6e7iPoo1P0MR
lxYNKo2yPtUYV/yEo48zAFaT6y9MWELY9FWX0w==

`pragma protect key_keyowner="Mentor Graphics Corporation", key_keyname="MGC-VELOCE-RSA", key_method="rsa"
`pragma protect encoding = (enctype="BASE64", line_length=76, bytes=128)
`pragma protect key_block
d4Ir9YmkpeWxfTLlPQYtgkUeaxN8B1i90JFB7P9JRLI2mXpcAqbM1Ddckph49f+F/oHMkaQ1Dzdy
Tej6kxJi/Wdiu5rZ5OmBuS1ZbOG2CJC6XfXj0ThvxQ1LW4KNfufD8drKKx2IixrN1qv0PX60j/6X
3tXvEQ4xFipk/uBl74M=

`pragma protect key_keyowner="Mentor Graphics Corporation", key_keyname="MGC-VERIF-SIM-RSA-2", key_method="rsa"
`pragma protect encoding = (enctype="BASE64", line_length=76, bytes=256)
`pragma protect key_block
AcG3M3dwdYa7Crux6whvnEB7jpQ3vYcVRjQE5IC/udJBxEWpsGpVQvccMKBkoDHqdapYFU/iis0y
URrcLRxuH1iKJfzTcPj3UrIKQD9hZrAokyeBmOtsQ+XAWjJkJU85Qm3Ik0ZRBpB/TLb4/lT75yA7
UVZ90xB7V73bMURI+0oh6pjmcYbZ1CLO3wNCtVzFBzmngbfwzsRdxSArLHEd3e5VZpxrrhdclpzu
0l0xLi8XYPn9IoQcyVJfd34Oj5C6xjuozB8+xokj5qXDryDzLxGuS1qWUi55uL8EBiv81cZoNk/O
K6JvjMhV3Byr7N02AfkTJtDyXNgRm5QsOdQIIQ==

`pragma protect key_keyowner="Real Intent", key_keyname="RI-RSA-KEY-1", key_method="rsa"
`pragma protect encoding = (enctype="BASE64", line_length=76, bytes=256)
`pragma protect key_block
s7hXRgGD7PplS4pBVEYIAD7ljzuh25HUgBtLBeE/2ImUhn/63TjM1VrWBdMEmMOCTVMAMtVjdkQW
NS+ZyPExJTiGBpj5ZS0pPGflQ6V7uW6IpfHQ6aa9mRriWcZ4TuEr3yMtE+luDo6Chw0hgizpV5By
lGPXBz9qv4Z/PSwxAtCxO/ksyRObQ9glxV/ECfAE/lIKYwJ+/WaCNIGStPhoMB6/bo6ZBAVbZ8wx
PuM5xkRe1qTNlQSqCRqnrSvSGG6JoxHfLwN4Y61rUk9XF6mr0zxKpwONVqkYd73dCWsbtsywPXhv
u4Gcx00Vud2slvSdQXyCJiSRTblaZrSdOApVCQ==

`pragma protect key_keyowner="Xilinx", key_keyname="xilinxt_2020_08", key_method="rsa"
`pragma protect encoding = (enctype="BASE64", line_length=76, bytes=256)
`pragma protect key_block
ZckK18NWTOr3bQxeTQ2Hmehew8edLI59NtFiD96pysefOkcdqoNSDc6Q21XYVaYLKX0lYNCW/c6n
fv5C4G0fE7A80b0SPkQE+sipaiBKWBNNb7GwGwwySLCePoDtZybeOvpqvvaxadDa0dqtQJbA4Zgj
LzcT0GMgIQgj84Z3Eu8ooI5jQk9jwAPKrZcdar/xrnoD2kI5ELzXQbNAj6Di5OEO91+HAv8WphCC
mruqWvwON3yyTxqzXEmugM0Ro7iCh5ErefC7ej8IJ8xoJ4++2UlBwwue5mPA5gNYhtQkFcQ7Np1e
Ycs+gyHI/UVizRd+96zJ57Sq5tf88tJ9NQqRfA==

`pragma protect key_keyowner="Metrics Technologies Inc.", key_keyname="DSim", key_method="rsa"
`pragma protect encoding = (enctype="BASE64", line_length=76, bytes=256)
`pragma protect key_block
Rws6+VMWmHV6kQwKOlrBwauV6Z4saZJvIT7vO0puMXJlcaRlIvoj5ogg/v58Ri3VQEE9fMChgryM
pyKqZnjLcwA7Y2k+uXNfhwaaHv00BPIfbb7kyG3qs00Ja2TNlJI4WJsoMo88a5AbTegYyaQ8vJaM
0GjbbTcOuG8re5lVCUM0FM1b/1k7+iQp6Klfmh9VtIYk5dhuAyQHMRFGmOSfdE27bffNgdfYS3kp
i0DtbgNnRIDsdIlu2/RO3GojLf+2oyIm6Zf4ORn5bjGq4hduIv0GFaYbpasBvNnpNjRbeA0hPZcR
ouMej74eTG4+j2Xu7Kl+tvKu2e2a0zAkb0Z6Cg==

`pragma protect key_keyowner="Mentor Graphics Corporation", key_keyname="MGC-PREC-RSA", key_method="rsa"
`pragma protect encoding = (enctype="BASE64", line_length=76, bytes=256)
`pragma protect key_block
FSaKCcW9XGTFhQRVbed5rCxVB56X4hjuZYrW8pWIo3FSle7fVVNNB1m4uastOlyjldLGVBxn+YGW
daSftGRAuf165M66vOIvsPXqKXD8l/ZVDNr30B8JcJYibjMclyDVSuN1y9huaphNkx7fOcJJ/V8u
/Qsjw6q62FWpxjoX1m1AEVwxyo7xS5KXXweieMN82h9M19rqld4LurOIebftdE5NheBMHoHRNS5v
S3ov7hzQkJ9KKQjuaGtcARfR0WnDm6cYDcAvUKDi8R+RzuCDadFZ83ET/r61srjBDRFk+VUx0E7+
PCxWFxftrxUu5MrPWBEpiBTUjHeYnzWG00p19Q==

`pragma protect key_keyowner="Synplicity", key_keyname="SYNP15_1", key_method="rsa"
`pragma protect encoding = (enctype="BASE64", line_length=76, bytes=256)
`pragma protect key_block
K2s0icIIIRzDBenUo/Hm60ad0SOq+/Jr5zatb+G5vIiHG5DS98kJGmtkteaQ3d4FOB/ZKFu+xPt2
XCWHakhTuI7CPq7k+SzDCNYepAQpjSWHekqh0QGXW41S4Y0Lvd1wm0dcCjyEjWYRrZGgNRHUSccU
qcTfi1Jr+SRdLspkG2fsSKI2Cz21prS12Ol/3Y/7YyElwh3c3mEkgopZS3AnRa61185LodJy+7WG
hiZgZcL3CMnXIIPNQXKCklt4GBJAWkMb6wMvBpu0LyGWNH8GYvxv+73688+jVRQribcKQfS40t3y
hTOJW0yhxTiuE/bBwFw/5hv3g9kwK3xs0b3rqQ==

`pragma protect data_method = "AES128-CBC"
`pragma protect encoding = (enctype = "BASE64", line_length = 76, bytes = 103488)
`pragma protect data_block
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
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
