simonyiszk/open-hf-sdr/vivado/ha5kfu_ws2/ha5kfu_ws2.srcs/sources_1/bd/top/ip/top_dds_compiler_0_0/top_dds_compiler_0_0_sim_netlist.vhdl

-- Copyright 1986-2020 Xilinx, Inc. All Rights Reserved.
-- --------------------------------------------------------------------------------
-- Tool Version: Vivado v.2020.2 (win64) Build 3064766 Wed Nov 18 09:12:45 MST 2020
-- Date        : Fri Feb 12 23:07:29 2021
-- Host        : RemoteApp running 64-bit major release  (build 9200)
-- Command     : write_vhdl -force -mode funcsim -rename_top top_dds_compiler_0_0 -prefix
--               top_dds_compiler_0_0_ top_dds_compiler_0_0_sim_netlist.vhdl
-- Design      : top_dds_compiler_0_0
-- Purpose     : This VHDL netlist is a functional simulation representation of the design and should not be modified or
--               synthesized. This netlist cannot be used for SDF annotated simulation.
-- Device      : xc7s6ftgb196-1
-- --------------------------------------------------------------------------------
`protect begin_protected
`protect version = 1
`protect encrypt_agent = "XILINX"
`protect encrypt_agent_info = "Xilinx Encryption Tool 2020.2"
`protect key_keyowner="Cadence Design Systems.", key_keyname="cds_rsa_key", key_method="rsa"
`protect encoding = (enctype="BASE64", line_length=76, bytes=64)
`protect key_block
ZhH7Or7GCAhAFpiSiK8r6sA7RwjJ9Tdii11EzwiypNpPn0r9A7rJiiZol84XxYNanpwTLFPRwdF3
O17/caqkTg==

`protect key_keyowner="Synopsys", key_keyname="SNPS-VCS-RSA-2", key_method="rsa"
`protect encoding = (enctype="BASE64", line_length=76, bytes=128)
`protect key_block
ojNAWo89+4CzZxOHvA45GVT0ANL90cKmvVUXXwDB3fYmp9A9JzMVd1jVDc2C6zq40HRJI3LCtqYa
SANm7EdbxrlwmiFka/Vi1pmGwcvpHiXNHqEL40Ybr2rzaDJ/8s1TFl1xPgk91nvMuEUJ7Zn2ncWy
O4fQj9khXHZjQEY0hCk=

`protect key_keyowner="Aldec", key_keyname="ALDEC15_001", key_method="rsa"
`protect encoding = (enctype="BASE64", line_length=76, bytes=256)
`protect key_block
ALgZm8VrZWZvRIch4Br8F+SMV+QwzLgh4lhQ7l513y3OWEbGpnpl2ftnp0u/2xp6nc3McskfP6nm
PJIcZIlaoKToyc9ZRjlnu3qXdjqRKZiEy2ry6na1WNvAIaoQUm6cedQIfaS44sUErPv5Hny28v01
jQKfzwV2u2/WdDSpq9G8hOJmD8cQ3zZchT3gKLO9morrDng3GunTKEfwYc3psoRS0ADCiN8q34xa
B0V0mmxTng2mAObVTR5v4uBWpsqq4e715mqrEjAgTT2TiRmhZA6iEH0d/cullajmHuhhllApBMPr
NQ7v5B4A3oTiYslgvPfU5+fjwE/t5C4ngf7cMQ==

`protect key_keyowner="ATRENTA", key_keyname="ATR-SG-2015-RSA-3", key_method="rsa"
`protect encoding = (enctype="BASE64", line_length=76, bytes=256)
`protect key_block
NqL8mDDVaKZ5Rhf5kFotnTPpOfKK0XotF1IfCUjg/fLWMIgs9842rKKunnwWG4yl52a73CWOqlIU
wym62ZKwHQvNIhDYV4et8nOJ/ssF4L531FMXWk+Ax18Dho+Deap2g0iGf+xYvOf58mhjEUs+4Lpb
l6JQqgQz0Qvcux7Nb7vhRavZyxh1+omPDBi0rWxmBAAx6/3ruQBSwQYJCOtZByjb7cyYwaK2a5O+
gc37qC3xTorqIs13YdItFsS1XcyP9S+H98hyqMQtkTj9WbauO5PJXF9TgC7AZZdA6e7iPoo1P0MR
lxYNKo2yPtUYV/yEo48zAFaT6y9MWELY9FWX0w==

`protect key_keyowner="Mentor Graphics Corporation", key_keyname="MGC-VELOCE-RSA", key_method="rsa"
`protect encoding = (enctype="BASE64", line_length=76, bytes=128)
`protect key_block
d4Ir9YmkpeWxfTLlPQYtgkUeaxN8B1i90JFB7P9JRLI2mXpcAqbM1Ddckph49f+F/oHMkaQ1Dzdy
Tej6kxJi/Wdiu5rZ5OmBuS1ZbOG2CJC6XfXj0ThvxQ1LW4KNfufD8drKKx2IixrN1qv0PX60j/6X
3tXvEQ4xFipk/uBl74M=

`protect key_keyowner="Mentor Graphics Corporation", key_keyname="MGC-VERIF-SIM-RSA-2", key_method="rsa"
`protect encoding = (enctype="BASE64", line_length=76, bytes=256)
`protect key_block
AcG3M3dwdYa7Crux6whvnEB7jpQ3vYcVRjQE5IC/udJBxEWpsGpVQvccMKBkoDHqdapYFU/iis0y
URrcLRxuH1iKJfzTcPj3UrIKQD9hZrAokyeBmOtsQ+XAWjJkJU85Qm3Ik0ZRBpB/TLb4/lT75yA7
UVZ90xB7V73bMURI+0oh6pjmcYbZ1CLO3wNCtVzFBzmngbfwzsRdxSArLHEd3e5VZpxrrhdclpzu
0l0xLi8XYPn9IoQcyVJfd34Oj5C6xjuozB8+xokj5qXDryDzLxGuS1qWUi55uL8EBiv81cZoNk/O
K6JvjMhV3Byr7N02AfkTJtDyXNgRm5QsOdQIIQ==

`protect key_keyowner="Real Intent", key_keyname="RI-RSA-KEY-1", key_method="rsa"
`protect encoding = (enctype="BASE64", line_length=76, bytes=256)
`protect key_block
s7hXRgGD7PplS4pBVEYIAD7ljzuh25HUgBtLBeE/2ImUhn/63TjM1VrWBdMEmMOCTVMAMtVjdkQW
NS+ZyPExJTiGBpj5ZS0pPGflQ6V7uW6IpfHQ6aa9mRriWcZ4TuEr3yMtE+luDo6Chw0hgizpV5By
lGPXBz9qv4Z/PSwxAtCxO/ksyRObQ9glxV/ECfAE/lIKYwJ+/WaCNIGStPhoMB6/bo6ZBAVbZ8wx
PuM5xkRe1qTNlQSqCRqnrSvSGG6JoxHfLwN4Y61rUk9XF6mr0zxKpwONVqkYd73dCWsbtsywPXhv
u4Gcx00Vud2slvSdQXyCJiSRTblaZrSdOApVCQ==

`protect key_keyowner="Xilinx", key_keyname="xilinxt_2020_08", key_method="rsa"
`protect encoding = (enctype="BASE64", line_length=76, bytes=256)
`protect key_block
ZckK18NWTOr3bQxeTQ2Hmehew8edLI59NtFiD96pysefOkcdqoNSDc6Q21XYVaYLKX0lYNCW/c6n
fv5C4G0fE7A80b0SPkQE+sipaiBKWBNNb7GwGwwySLCePoDtZybeOvpqvvaxadDa0dqtQJbA4Zgj
LzcT0GMgIQgj84Z3Eu8ooI5jQk9jwAPKrZcdar/xrnoD2kI5ELzXQbNAj6Di5OEO91+HAv8WphCC
mruqWvwON3yyTxqzXEmugM0Ro7iCh5ErefC7ej8IJ8xoJ4++2UlBwwue5mPA5gNYhtQkFcQ7Np1e
Ycs+gyHI/UVizRd+96zJ57Sq5tf88tJ9NQqRfA==

`protect key_keyowner="Metrics Technologies Inc.", key_keyname="DSim", key_method="rsa"
`protect encoding = (enctype="BASE64", line_length=76, bytes=256)
`protect key_block
Rws6+VMWmHV6kQwKOlrBwauV6Z4saZJvIT7vO0puMXJlcaRlIvoj5ogg/v58Ri3VQEE9fMChgryM
pyKqZnjLcwA7Y2k+uXNfhwaaHv00BPIfbb7kyG3qs00Ja2TNlJI4WJsoMo88a5AbTegYyaQ8vJaM
0GjbbTcOuG8re5lVCUM0FM1b/1k7+iQp6Klfmh9VtIYk5dhuAyQHMRFGmOSfdE27bffNgdfYS3kp
i0DtbgNnRIDsdIlu2/RO3GojLf+2oyIm6Zf4ORn5bjGq4hduIv0GFaYbpasBvNnpNjRbeA0hPZcR
ouMej74eTG4+j2Xu7Kl+tvKu2e2a0zAkb0Z6Cg==

`protect key_keyowner="Mentor Graphics Corporation", key_keyname="MGC-PREC-RSA", key_method="rsa"
`protect encoding = (enctype="BASE64", line_length=76, bytes=256)
`protect key_block
UI6cHb/j3uqiaJtHwkLCyNfq21SmQUbZdsYEaiC9l2dV7/C48PTcOPLsSkgBr95SIef0rAgFdl++
jeU1jYKQd0ce2zb2pxU5V2AlhOcGmHywZi3ZCZw9mwbx7Nv8fhaEIoUby8HXxL89vn8Xl/iagpmz
sjTe8BBAv0U5R6fPiQ4XiHoUkfBnPo+IM9+eVqhwKQ0q2pu5vn1jTzO4/3reO9ca4eL3Y00PZoPE
tMbUzukJVV+gqalsnFU2mHQvEnHxFnxuPyOfAwav4fu48SpR2fr+I997xGI48JZJ8kUKxy/mAuF6
+X8ks0zIEh/9qTtuLiVdy2HGdiYVtaNBaP5n5A==

`protect key_keyowner="Synplicity", key_keyname="SYNP15_1", key_method="rsa"
`protect encoding = (enctype="BASE64", line_length=76, bytes=256)
`protect key_block
WNFVDJT0lK4TMFMLmNqi57yzqN02+NURmkQwTmcYpwuvDKl0IbI+yqgi263qtMw3gCSE7oXJbNHF
cEfIbAuw3ob5XzE2iqmVfs7U1iRgtlCDiPxnCc2RLGETyBuRZDVs4NNJVBZp6VrxMVOKDLcMuL7Y
laK2Ydk58QkQxIRAEsNPsmfLw3CBN69ZmKkELEg8QPtg3R9uJ+Ok91CNrlR90vFTtL4cTw+3uHsb
+gutudXR9zu1/832Y/p0LCNuKNqvMLfMDwSNZWxUvV9TFc2lapzOLBR9gzCuwVaFPsBMBAe1iBN1
MWJh1AxC+tT98qt8Ch7qJacrFcYTDdM78FB7uQ==

`protect data_method = "AES128-CBC"
`protect encoding = (enctype = "BASE64", line_length = 76, bytes = 142560)
`protect data_block
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
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
